noaa-afsc-mace/FSVPAD-hydrophones/Technical documentation/radioconfiguration/RX_1.png

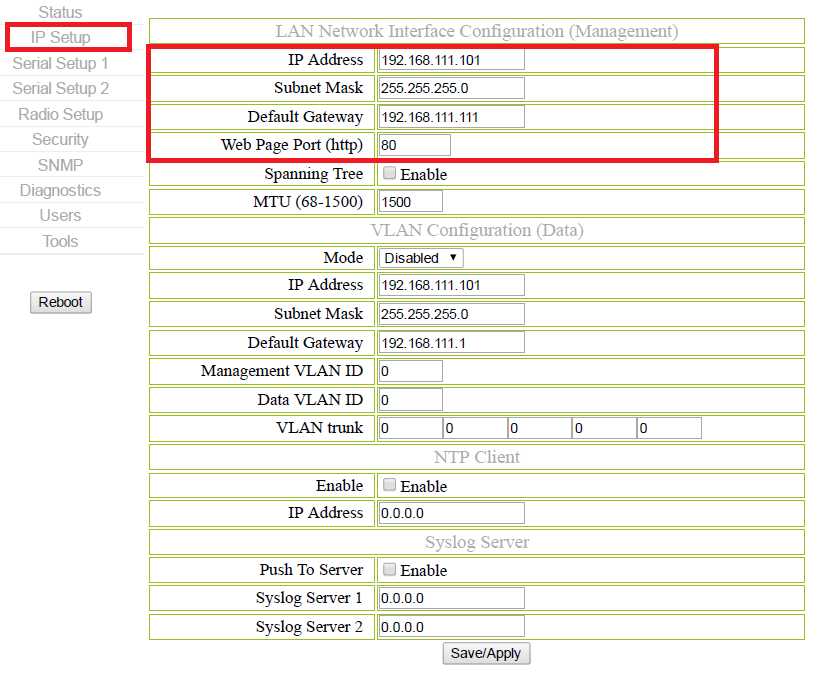
Technical documentation/radioconfiguration/RX_1.png
