noaa-afsc-mace/FSVPAD-hydrophones/Technical documentation/radioconfiguration/RX_2.png

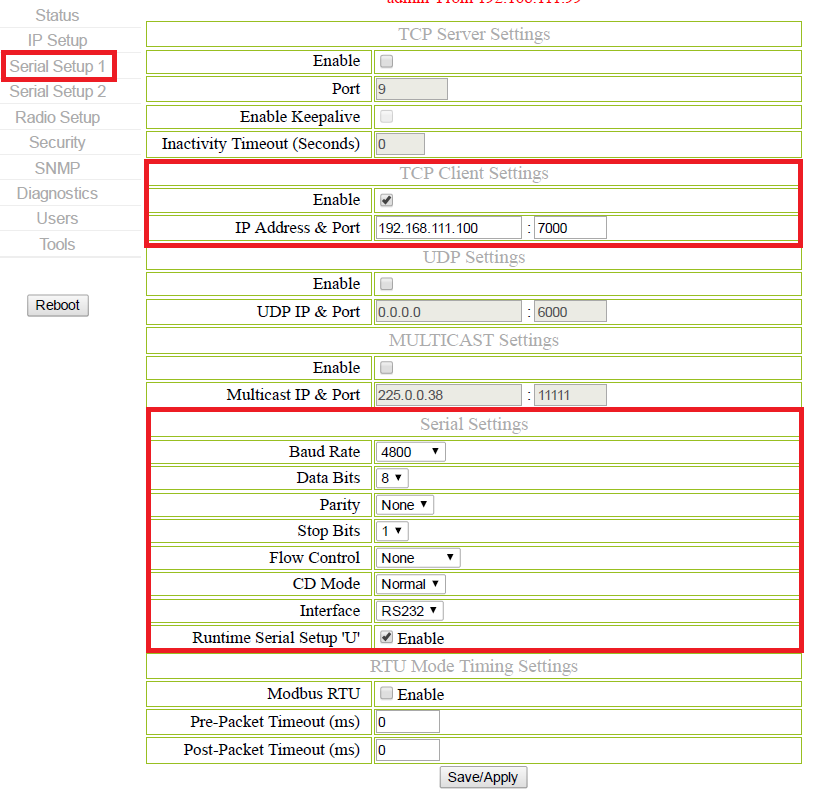
Technical documentation/radioconfiguration/RX_2.png
