noaa-afsc-mace/FSVPAD-hydrophones/Technical documentation/radioconfiguration/RX_3.png

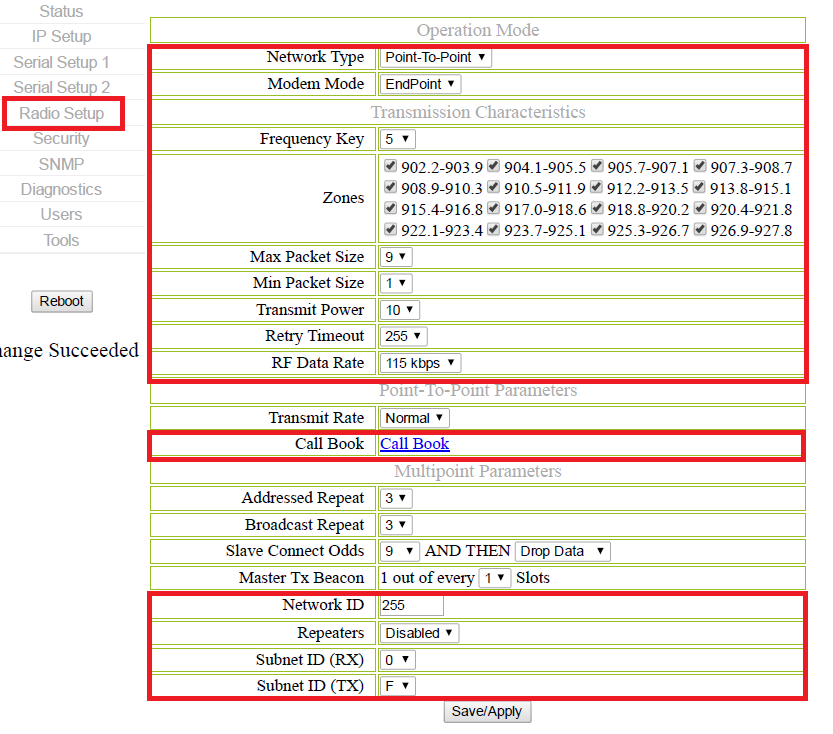
Technical documentation/radioconfiguration/RX_3.png
