noaa-afsc-mace/FSVPAD-hydrophones/Technical documentation/radioconfiguration/RX_4.png

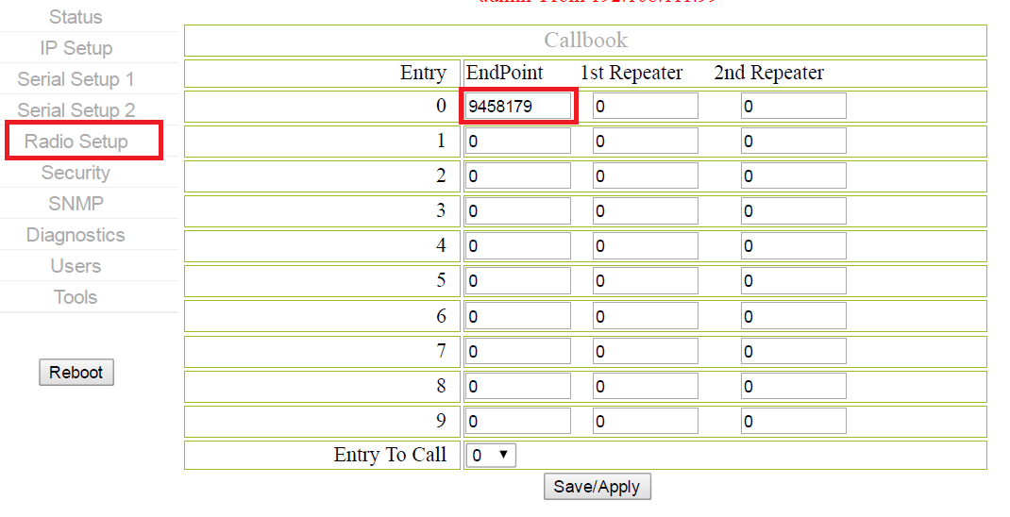
Technical documentation/radioconfiguration/RX_4.png
