noaa-afsc-mace/FSVPAD-hydrophones/Technical documentation/radioconfiguration/TX_1.png

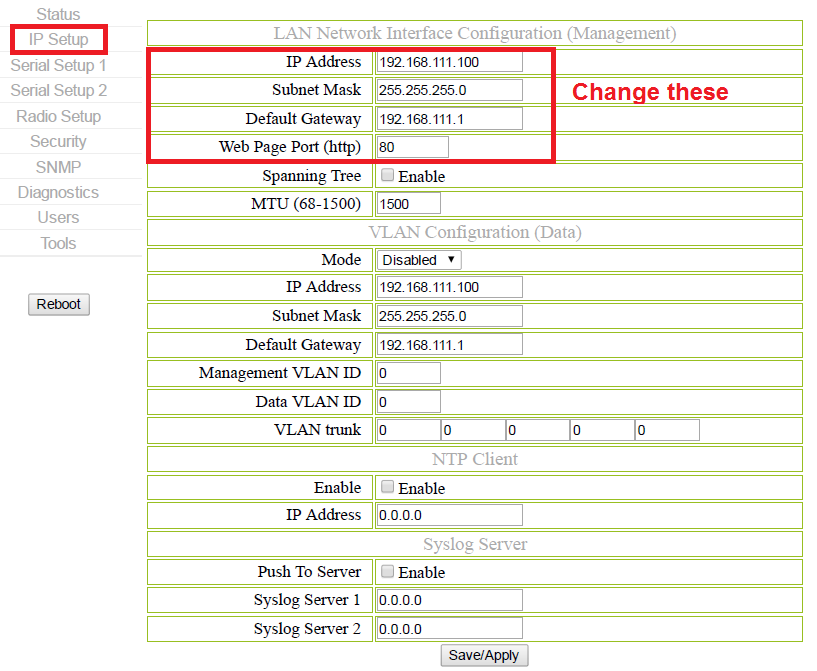
Technical documentation/radioconfiguration/TX_1.png
