noaa-afsc-mace/FSVPAD-hydrophones/Technical documentation/radioconfiguration/TX_2.png

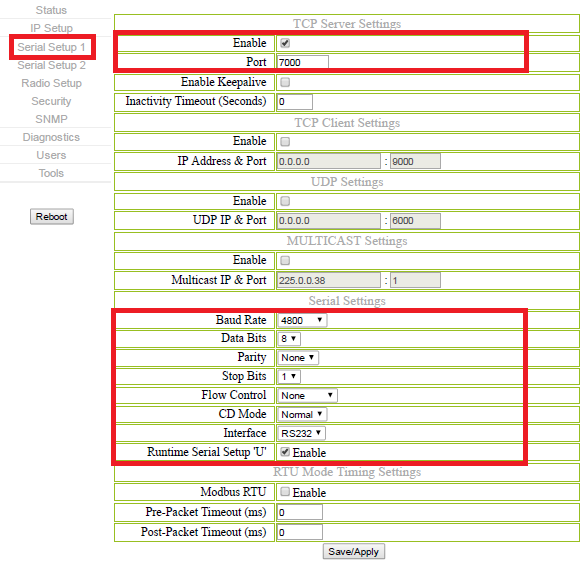
Technical documentation/radioconfiguration/TX_2.png
