noaa-afsc-mace/FSVPAD-hydrophones/Technical documentation/radioconfiguration/TX_3.png

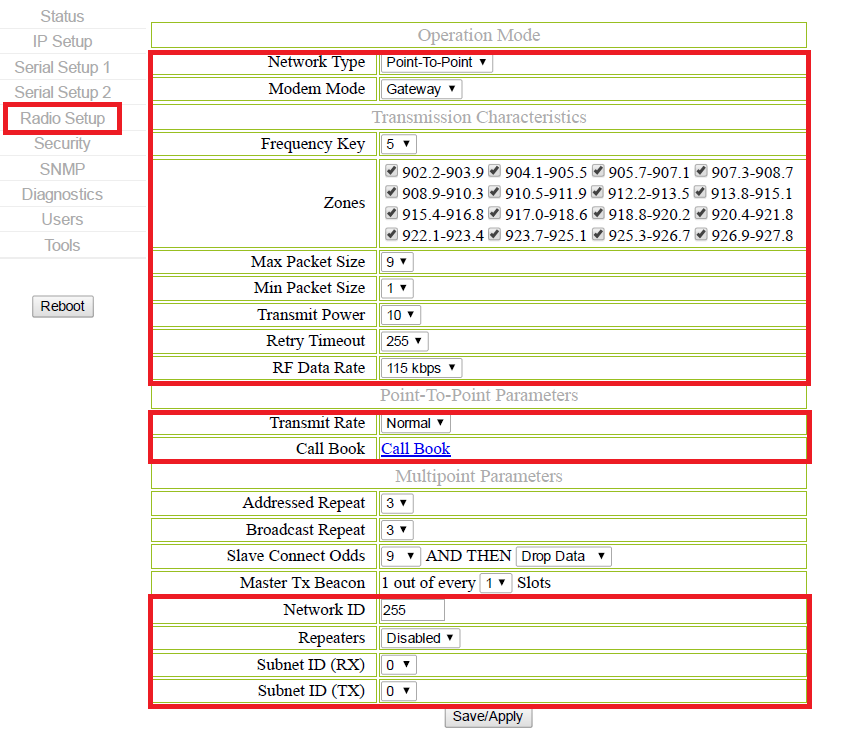
Technical documentation/radioconfiguration/TX_3.png
