noaa-afsc-mace/FSVPAD-hydrophones/Technical documentation/radioconfiguration/TX_4.png

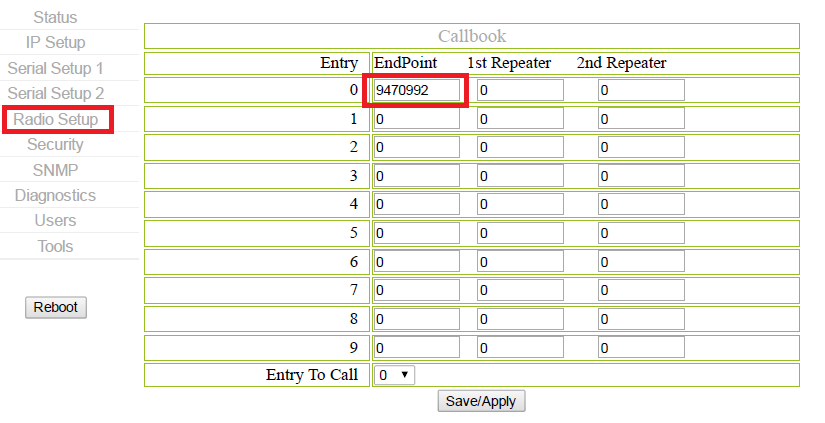
Technical documentation/radioconfiguration/TX_4.png
