noaa-afsc-mace/FSVPAD-hydrophones/Technical documentation/Subsystemdrawings/Electronics_side.png

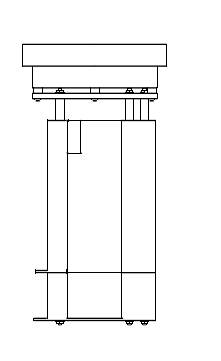
Technical documentation/Subsystemdrawings/Electronics_side.png
