noaa-afsc-mace/FSVPAD-hydrophones/Technical documentation/Subsystemdrawings/Mounting_Plate_noDims.png

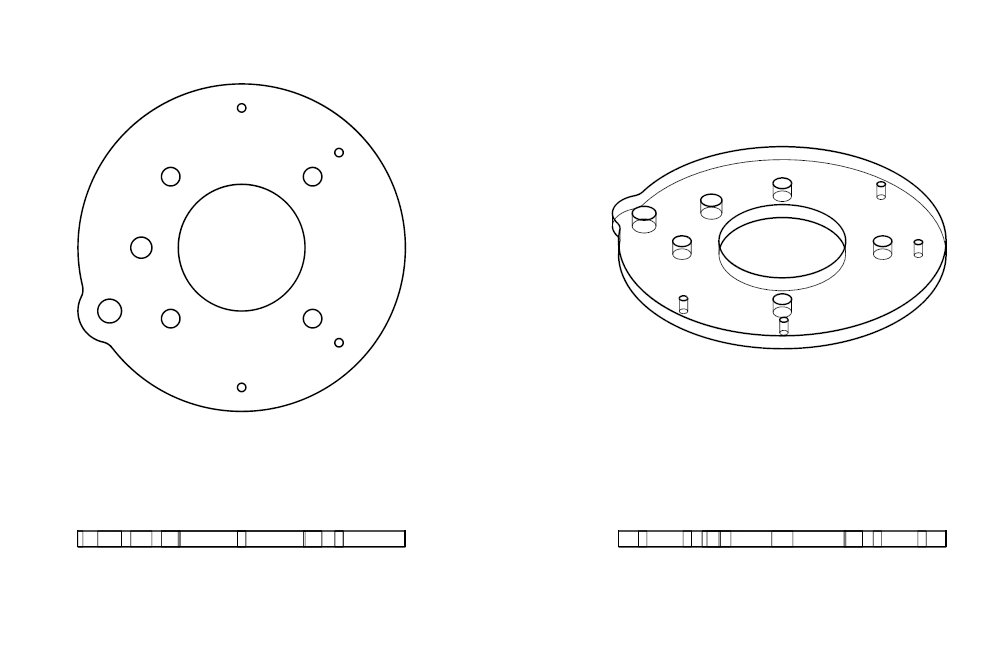
Technical documentation/Subsystemdrawings/Mounting_Plate_noDims.png
