noaa-afsc-mace/FSVPAD-hydrophones/Technical documentation/Subsystemdrawings/Sch 80 6 inch pipe flange.gif

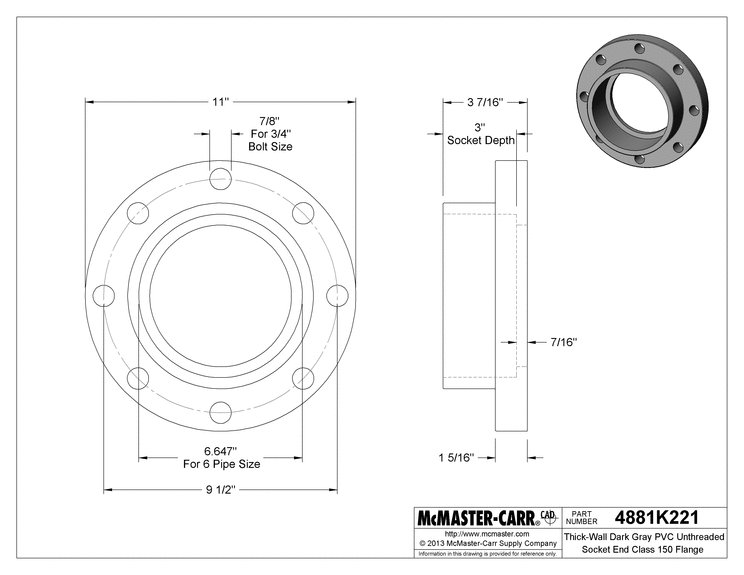
Technical documentation/Subsystemdrawings/Sch 80 6 inch pipe flange.gif
