noaa-afsc-mace/FSVPAD-hydrophones/Technical documentation/Subsystemdrawings/Strongback_Clamps.FCStd

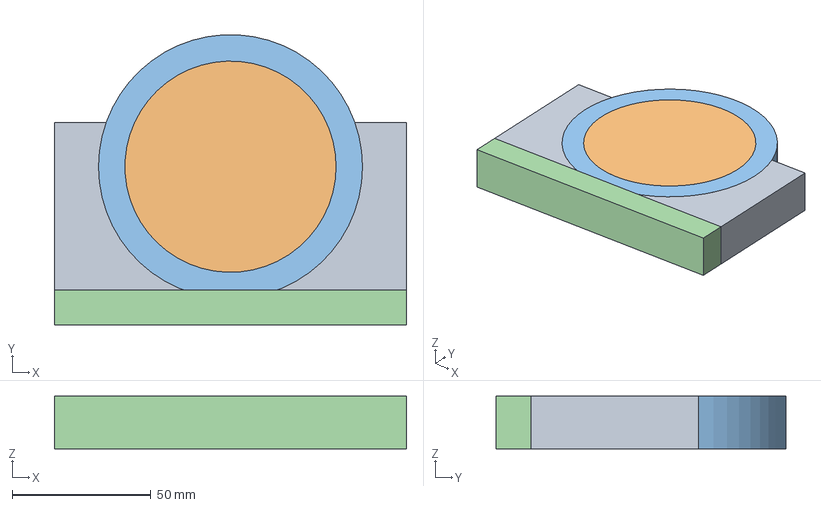
[picture p33: CAD file, 2024-04-29]
Technical documentation/Subsystemdrawings/Strongback_Clamps.FCStd
127.0 x 104.7 x 19.1 mm
Rectangle1
Cylindersmall
Cylinderlarge
