noaa-afsc-mace/FSVPAD-hydrophones/Technical documentation/Housingdrawings/HousingBot.stl

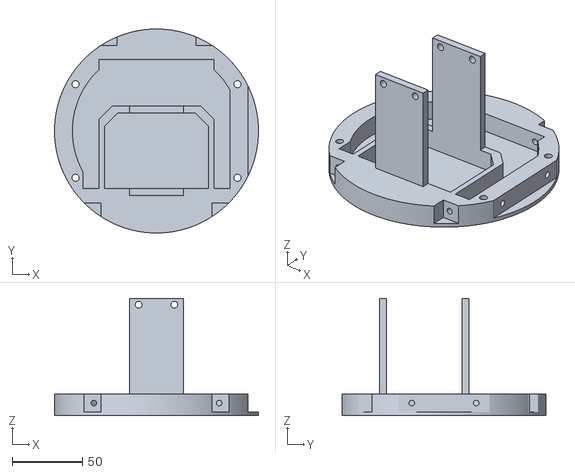
[picture p34: CAD file, 2024-04-29]
Technical documentation/Housingdrawings/HousingBot.stl
144.8 x 144.8 x 83.2
