noaa-afsc-mace/FSVPAD-hydrophones/Technical documentation/Subsystemdrawings/Strongback.FCStd

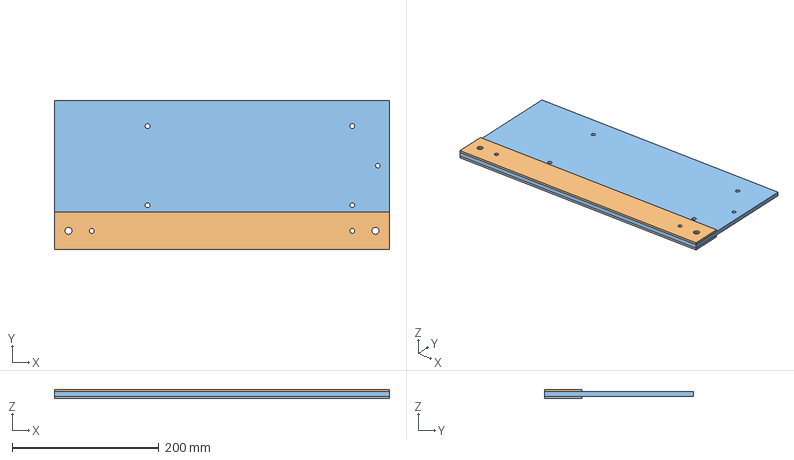
[picture p35: CAD file, 2024-04-29]
Technical documentation/Subsystemdrawings/Strongback.FCStd
457.2 x 203.2 x 12.7 mm
SS_holes1
SS_holes2
