noaa-afsc-mace/FSVPAD-hydrophones/Technical documentation/Housingdrawings/Top.stl

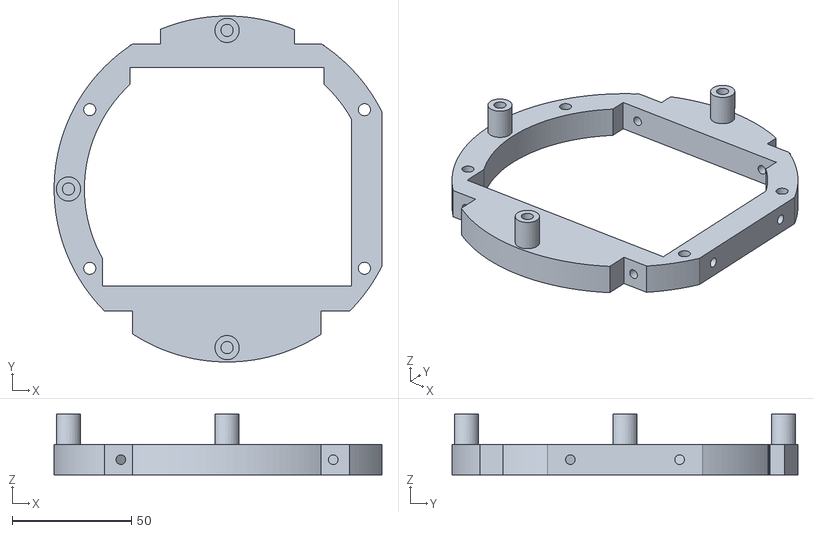
[picture p36: CAD file, 2024-04-29]
Technical documentation/Housingdrawings/Top.stl
137.1 x 144.8 x 25.4
