noaa-afsc-mace/FSVPAD-hydrophones/Technical documentation/Subsystemdrawings/Antenna_Stopper.FCStd

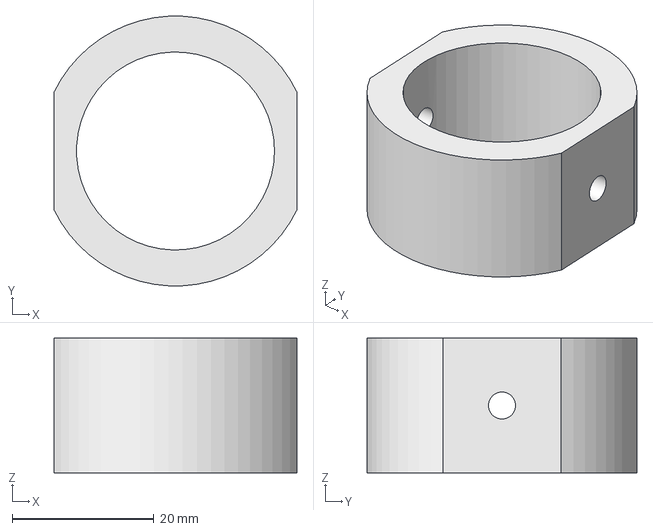
[picture p37: CAD file, 2024-04-29]
Technical documentation/Subsystemdrawings/Antenna_Stopper.FCStd
34.3 x 38.0 x 19.1 mm
