noaa-afsc-mace/FSVPAD-hydrophones/Technical documentation/Subsystemdrawings/LightFixtureB.FCStd

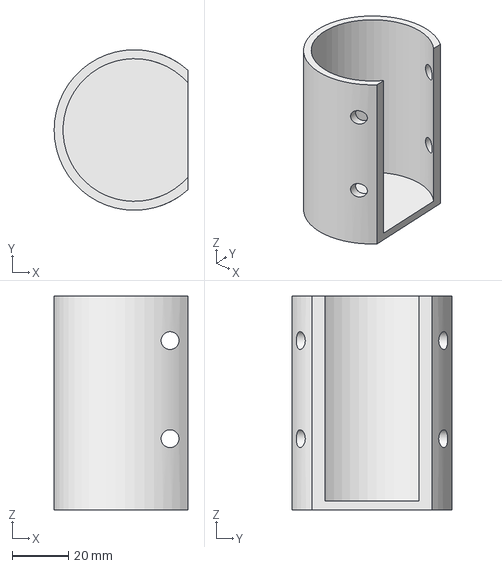
[picture p38: CAD file, 2024-04-29]
Technical documentation/Subsystemdrawings/LightFixtureB.FCStd
47.6 x 57.1 x 76.2 mm
