noaa-afsc-mace/FSVPAD-hydrophones/Technical documentation/Subsystemdrawings/Delrin_Cap.FCStd

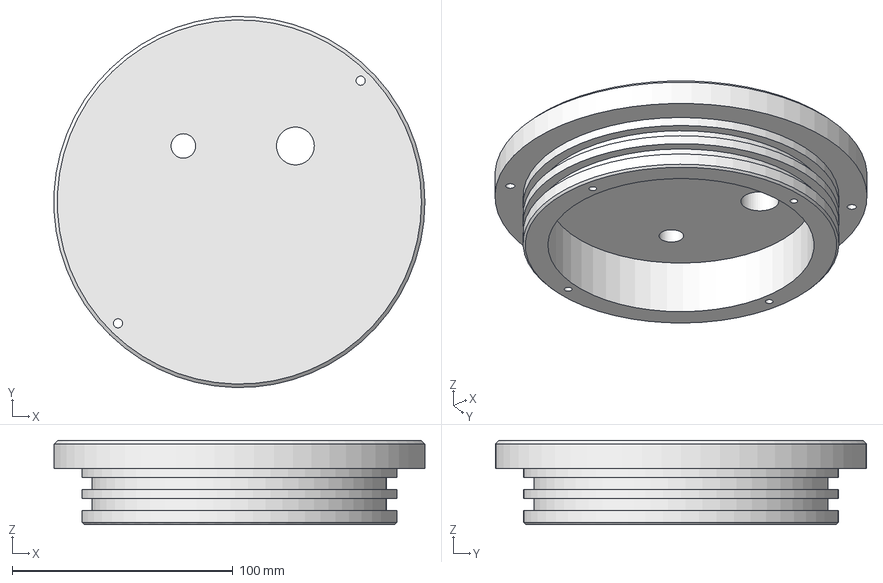
[picture p39: CAD file, 2024-04-29]
Technical documentation/Subsystemdrawings/Delrin_Cap.FCStd
168.2 x 168.2 x 38.1 mm
