noaa-afsc-mace/FSVPAD-hydrophones/Technical documentation/Subsystemdrawings/HeavePlate.FCStd

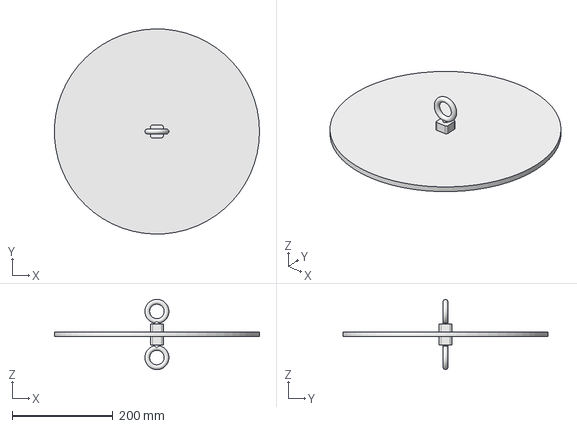
[picture p40: CAD file, 2024-04-29]
Technical documentation/Subsystemdrawings/HeavePlate.FCStd
406.1 x 406.3 x 139.1 mm
