noaa-afsc-mace/FSVPAD-hydrophones/Technical documentation/Subsystemdrawings/Strongback_Assesmbly_w_Clamps.FCStd

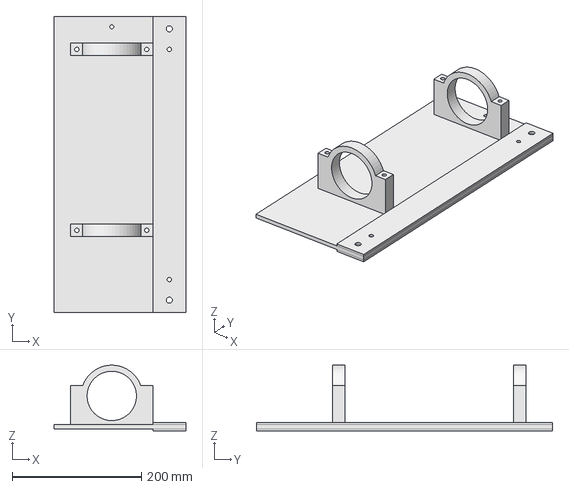
[picture p41: CAD file, 2024-04-29]
Technical documentation/Subsystemdrawings/Strongback_Assesmbly_w_Clamps.FCStd
203.2 x 457.2 x 101.6 mm
