noaa-afsc-mace/FSVPAD-hydrophones/Technical documentation/Subsystemdrawings/Strongback_Assesmbly_w_Clampsandhydrophones.FCStd

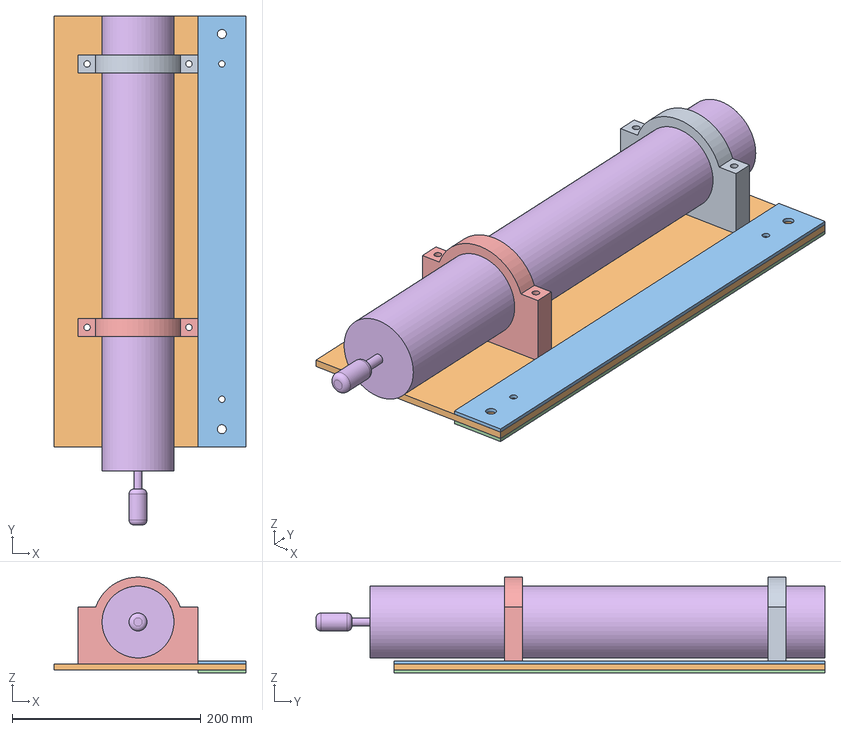
[picture p42: CAD file, 2024-04-29]
Technical documentation/Subsystemdrawings/Strongback_Assesmbly_w_Clampsandhydrophones.FCStd
203.2 x 539.8 x 101.6 mm
DelrinClamp
SS_holes2
SS_holes1
DelrinClamp2
Hydrophone
