noaa-afsc-mace/FSVPAD-hydrophones/Technical documentation/Subsystemdrawings/Exploded with light and antenna.FCStd

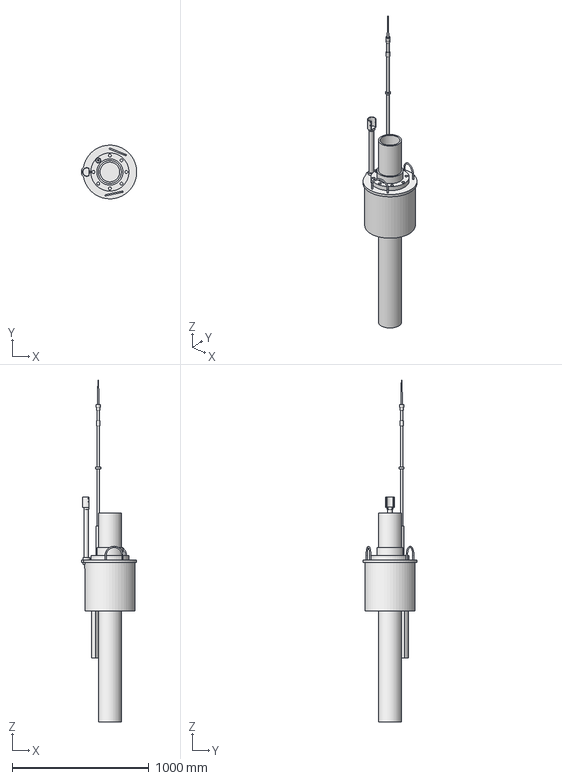
[picture p43: CAD file, 2024-04-29]
Technical documentation/Subsystemdrawings/Exploded with light and antenna.FCStd
406.4 x 393.4 x 2505.1 mm
