noaa-afsc-mace/FSVPAD-hydrophones/Technical documentation/Subsystemdrawings/Antenna_Top.FCStd

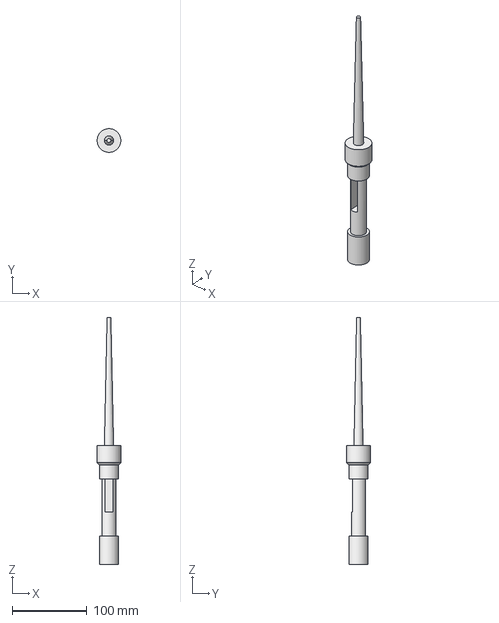
[picture p44: CAD file, 2024-04-29]
Technical documentation/Subsystemdrawings/Antenna_Top.FCStd
31.7 x 31.7 x 330.2 mm
