noaa-afsc-mace/FSVPAD-hydrophones/Technical documentation/Subsystemdrawings/Strongbacks_and_lines_SinglePoart.FCStd

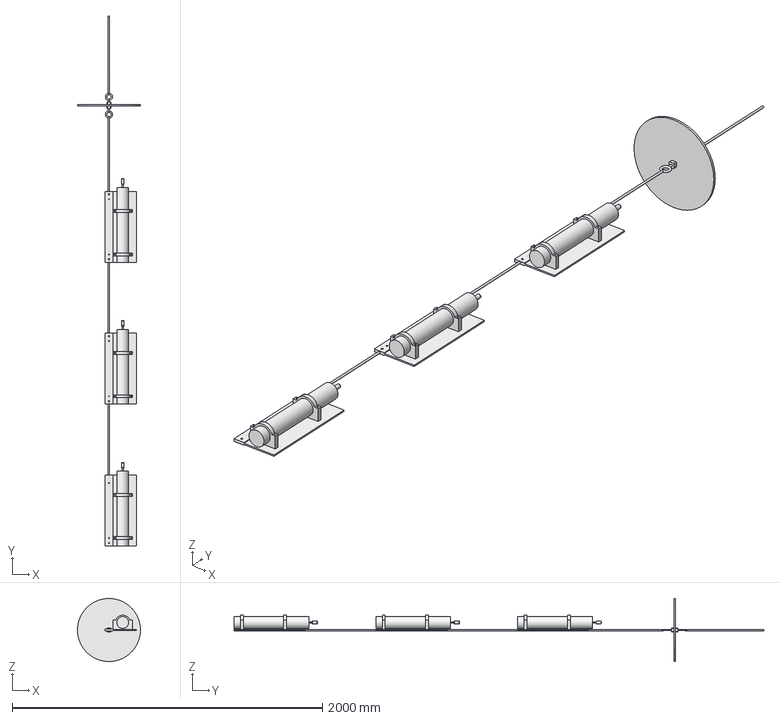
[picture p45: CAD file, 2024-04-29]
Technical documentation/Subsystemdrawings/Strongbacks_and_lines_SinglePoart.FCStd
406.0 x 3416.3 x 406.2 mm
