noaa-afsc-mace/FSVPAD-hydrophones/Technical documentation/Subsystemdrawings/MountingPlate.FCStd

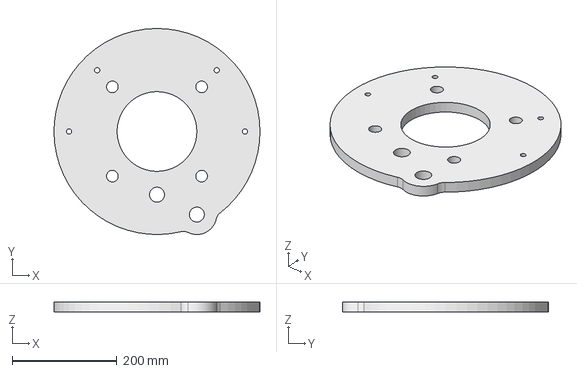
[picture p46: CAD file, 2024-04-29]
Technical documentation/Subsystemdrawings/MountingPlate.FCStd
393.7 x 393.7 x 19.1 mm
