noaa-afsc-mace/FSVPAD-hydrophones/Technical documentation/Subsystemdrawings/Strongback_Clamps2.FCStd

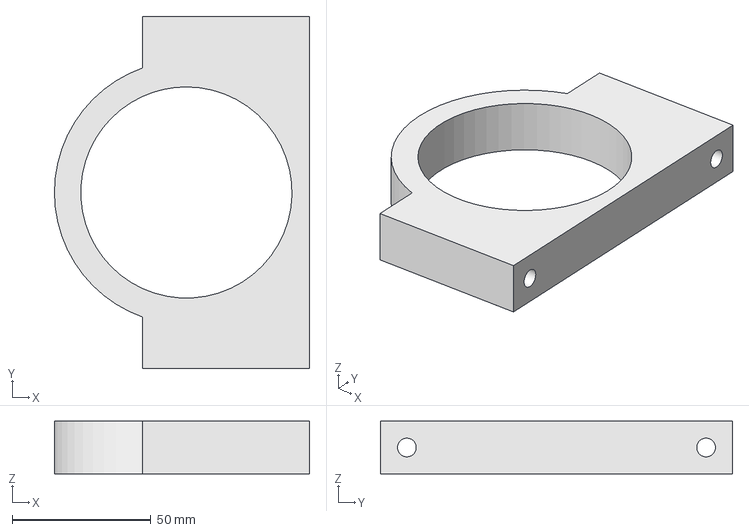
[picture p47: CAD file, 2024-04-29]
Technical documentation/Subsystemdrawings/Strongback_Clamps2.FCStd
92.1 x 127.0 x 19.1 mm
