noaa-afsc-mace/FSVPAD-hydrophones/Technical documentation/Subsystemdrawings/Antenna_PipeFoam.FCStd

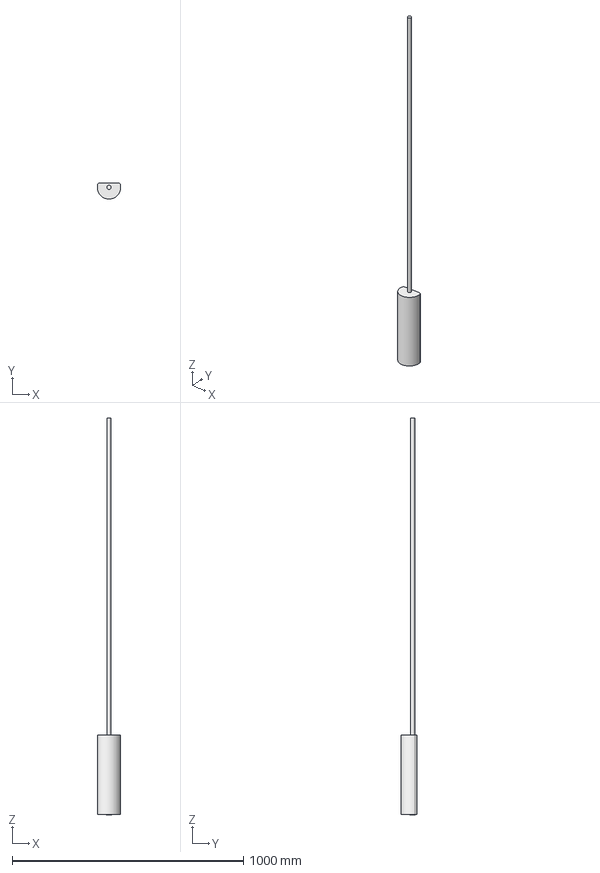
[picture p48: CAD file, 2024-04-29]
Technical documentation/Subsystemdrawings/Antenna_PipeFoam.FCStd
101.6 x 69.8 x 1717.0 mm
