noaa-afsc-mace/FSVPAD-hydrophones/Technical documentation/Subsystemdrawings/LightFixtureStopper.FCStd

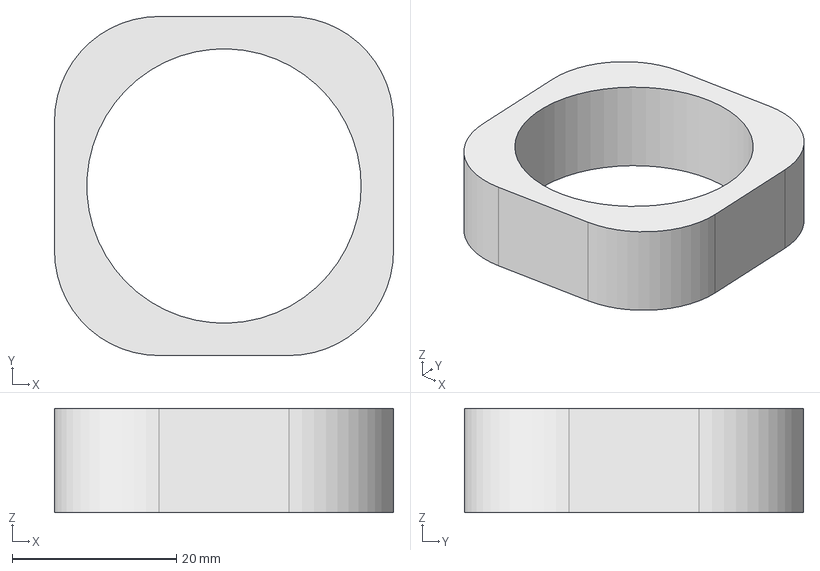
[picture p49: CAD file, 2024-04-29]
Technical documentation/Subsystemdrawings/LightFixtureStopper.FCStd
41.3 x 41.3 x 12.7 mm
