noaa-afsc-mace/FSVPAD-hydrophones/Example results/Ambient_vs_CPA.png

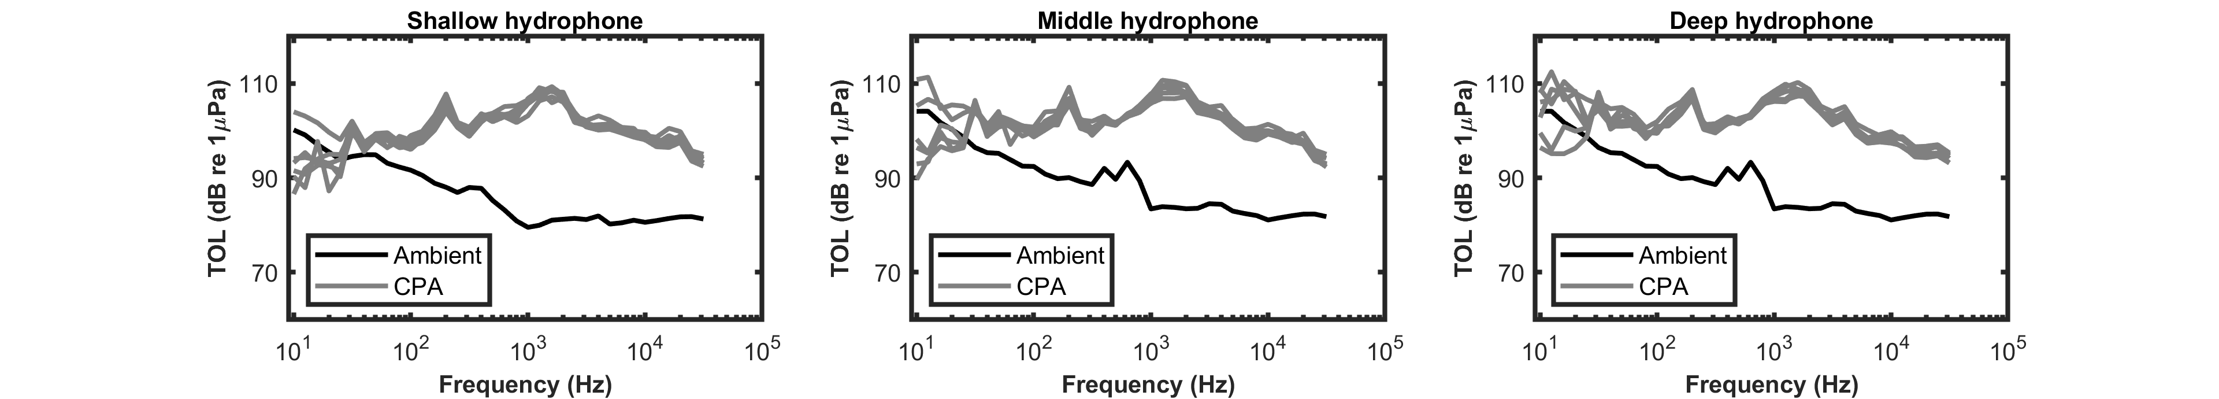
Example results/Ambient_vs_CPA.png
