noaa-afsc-mace/FSVPAD-hydrophones/Example results/CPA_and_TOL.png

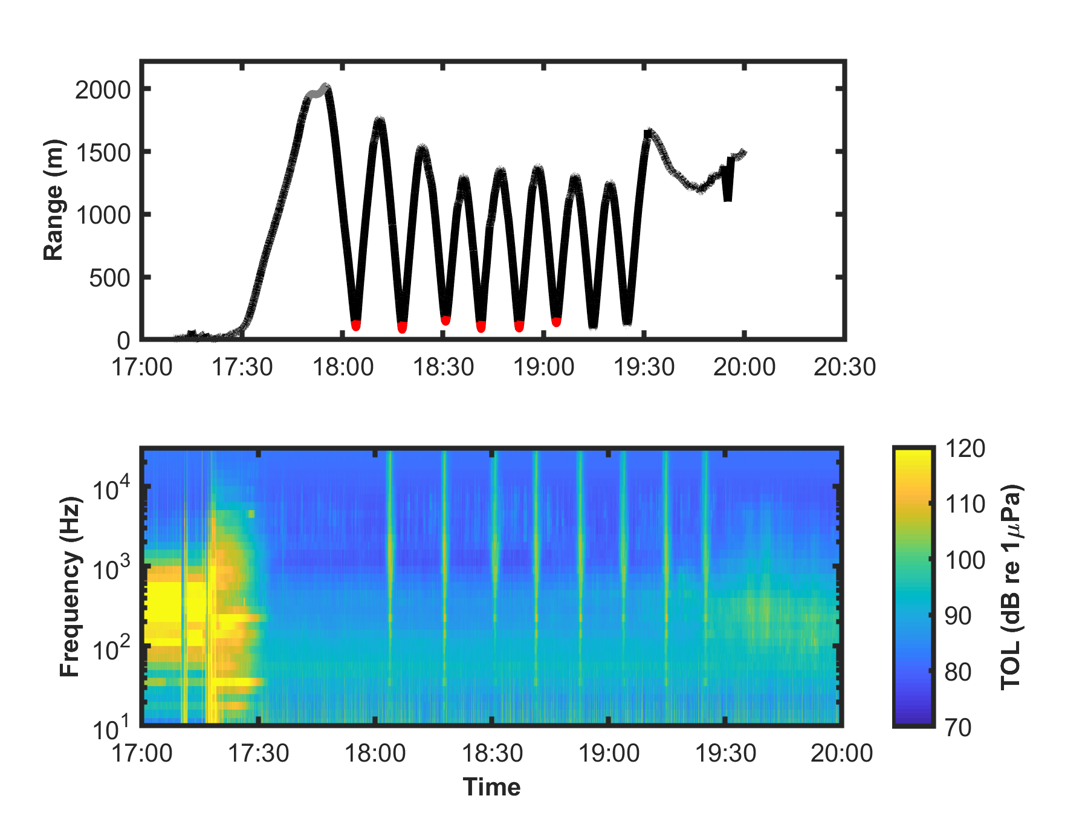
Example results/CPA_and_TOL.png
