noaa-afsc-mace/FSVPAD-hydrophones/Example results/DY_11knot_radiated_noise_comparison.png

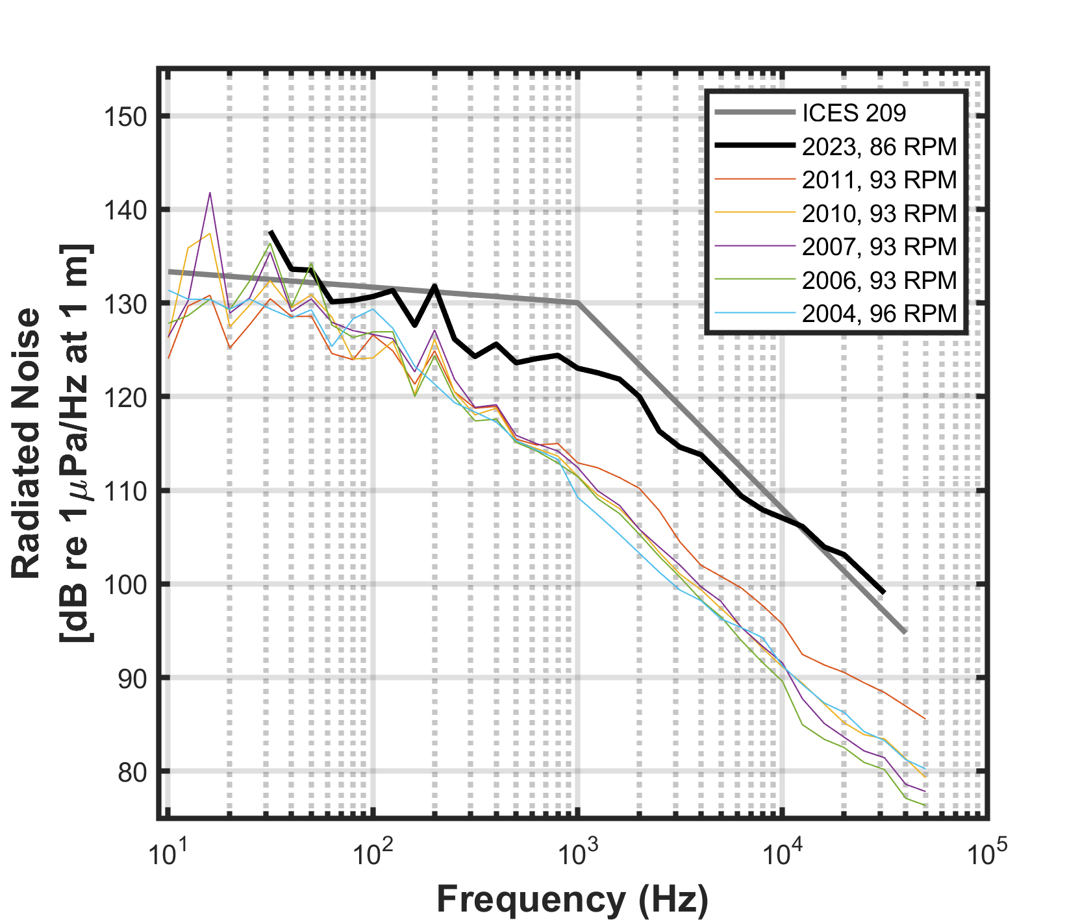
Example results/DY_11knot_radiated_noise_comparison.png
