noaa-afsc-mace/FSVPAD-hydrophones/Example results/FORMAL_Noise_Test_SNRs.png

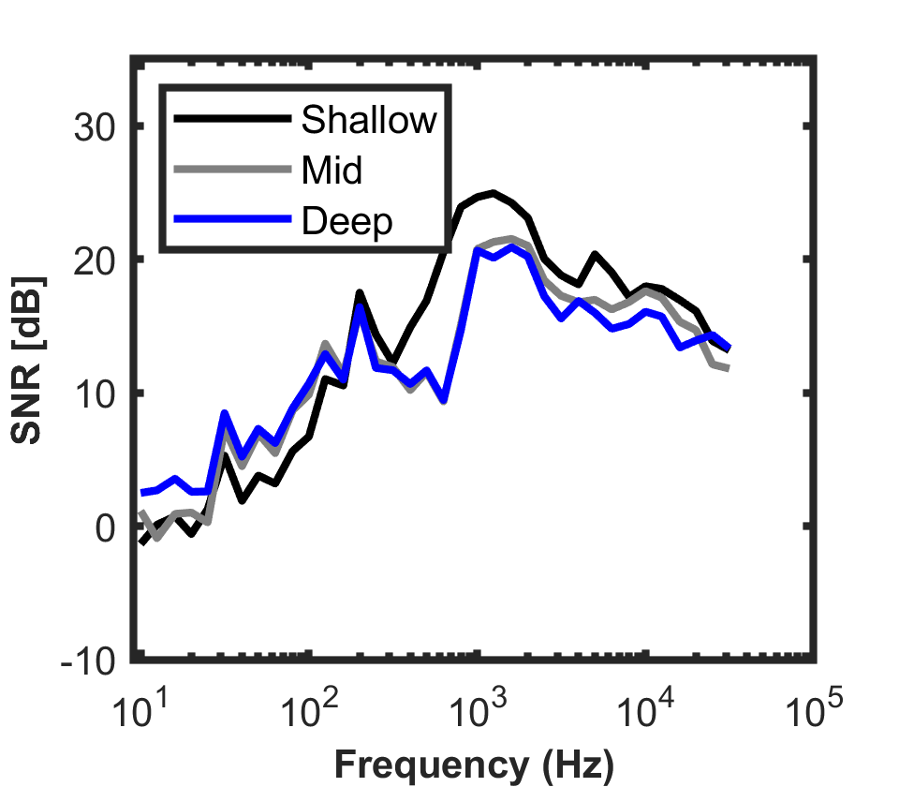
Example results/FORMAL_Noise_Test_SNRs.png
