noaa-afsc-mace/FSVPAD-hydrophones/Example results/FORMAL_Radiated_Noise.png

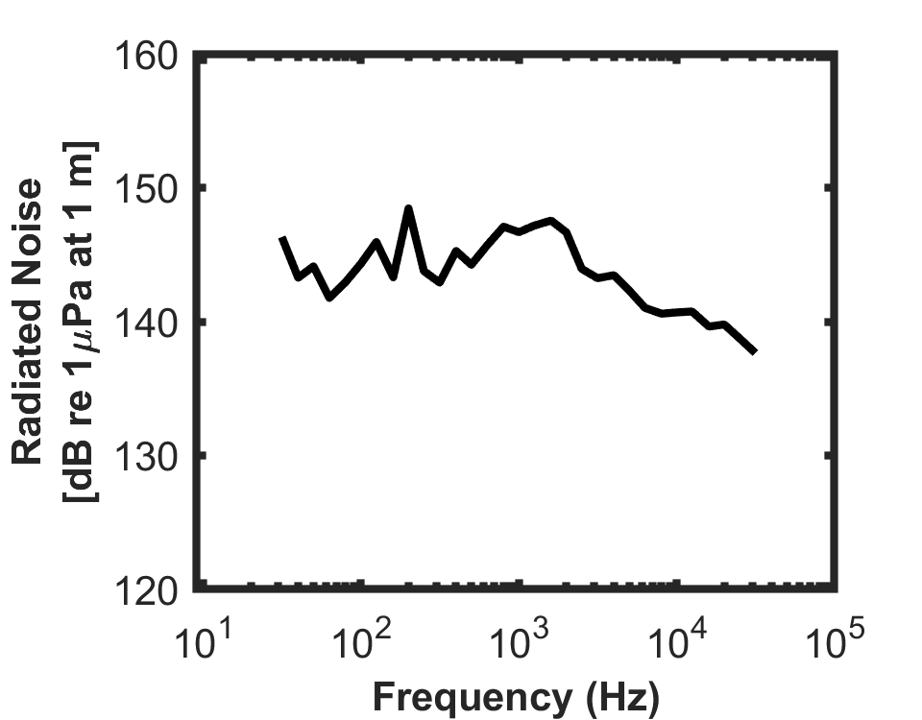
Example results/FORMAL_Radiated_Noise.png
