noaa-afsc-mace/FSVPAD-hydrophones/Example results/Noise_Test_SNRs.png

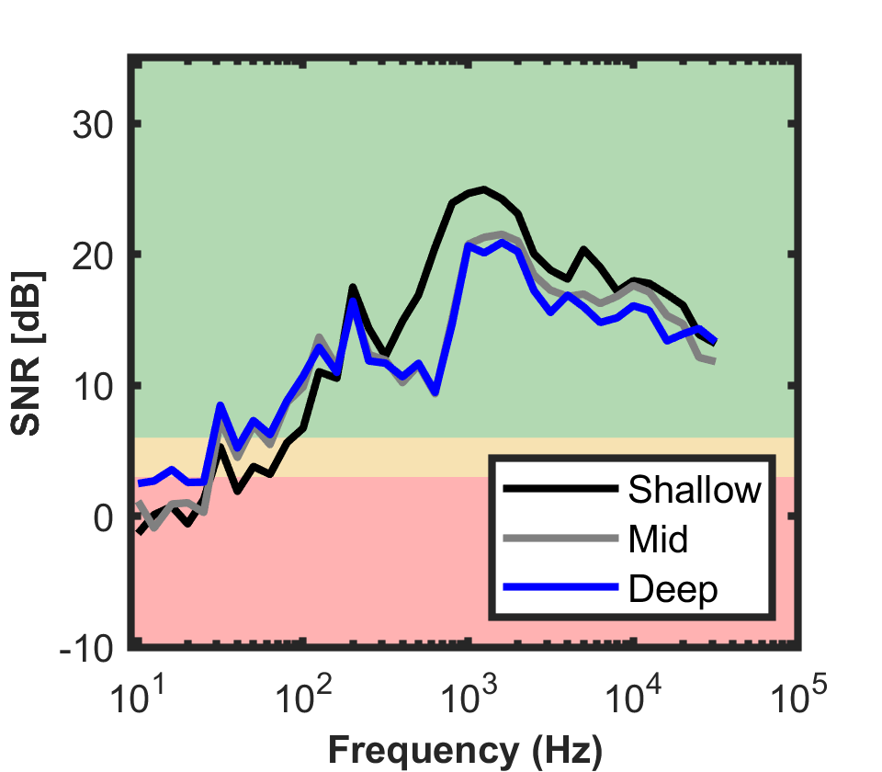
Example results/Noise_Test_SNRs.png
