noaa-afsc-mace/FSVPAD-hydrophones/Example results/RadiatedNoise_All_Passes.png

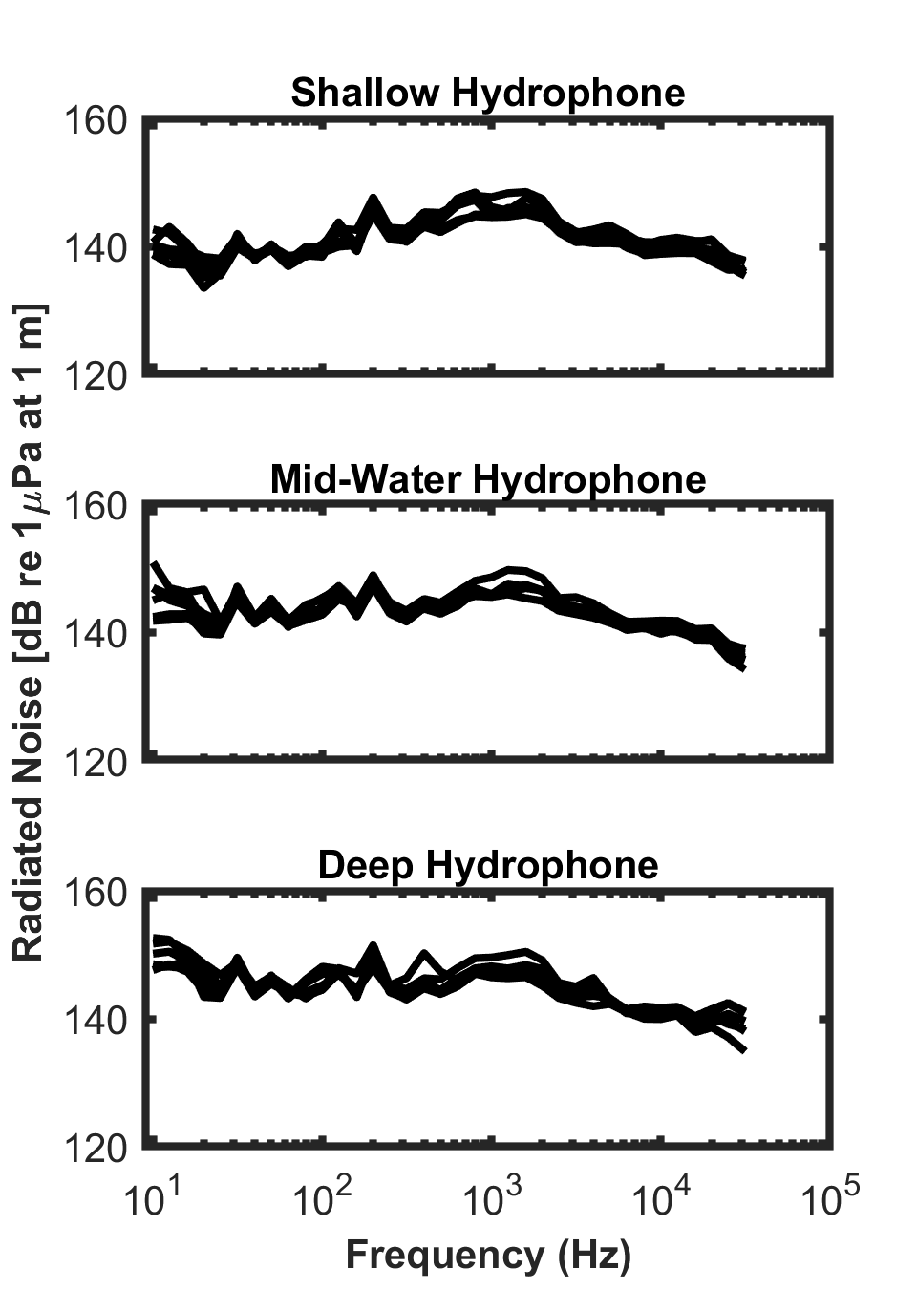
Example results/RadiatedNoise_All_Passes.png
