noaa-afsc-mace/FSVPAD-hydrophones/Example results/Range_of_Noise.png

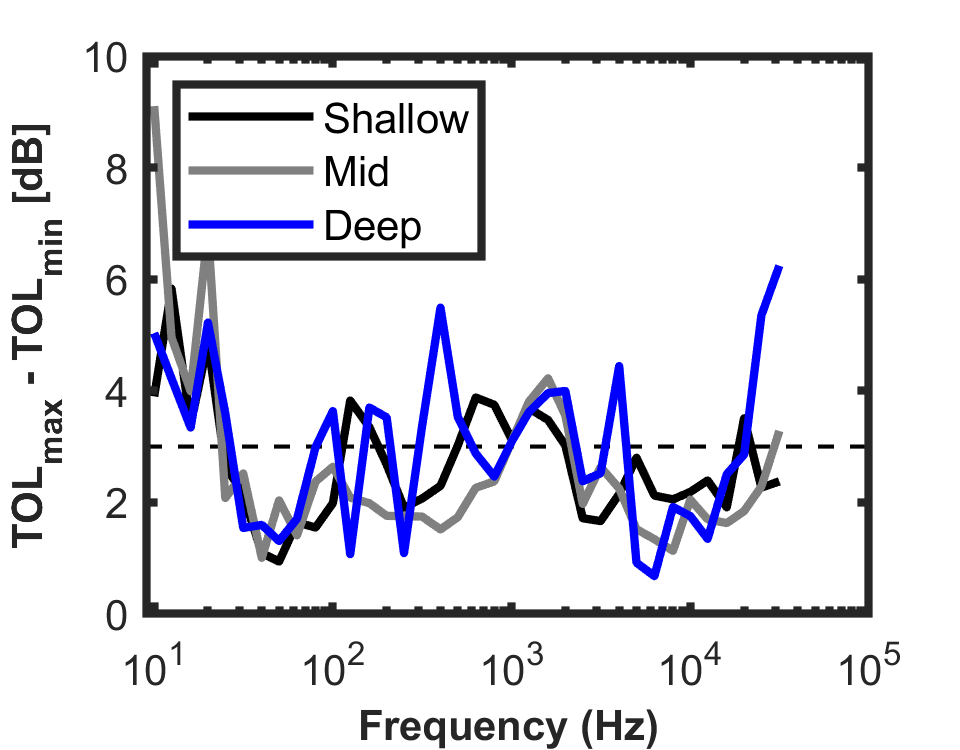
Example results/Range_of_Noise.png
