noaa-afsc-mace/FSVPAD-hydrophones/Example results/Result_overview_vs_ICES_SPEC.png

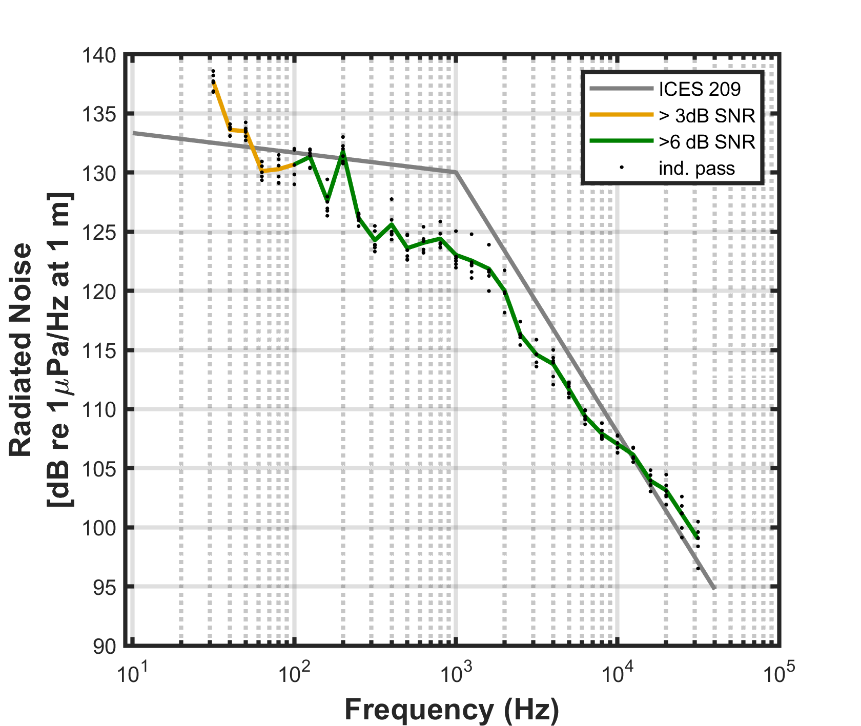
Example results/Result_overview_vs_ICES_SPEC.png
