noaa-afsc-mace/FSVPAD-hydrophones/Technical documentation/PistonphoneCalibration/SN_382313_Cal_TimeSeries.png

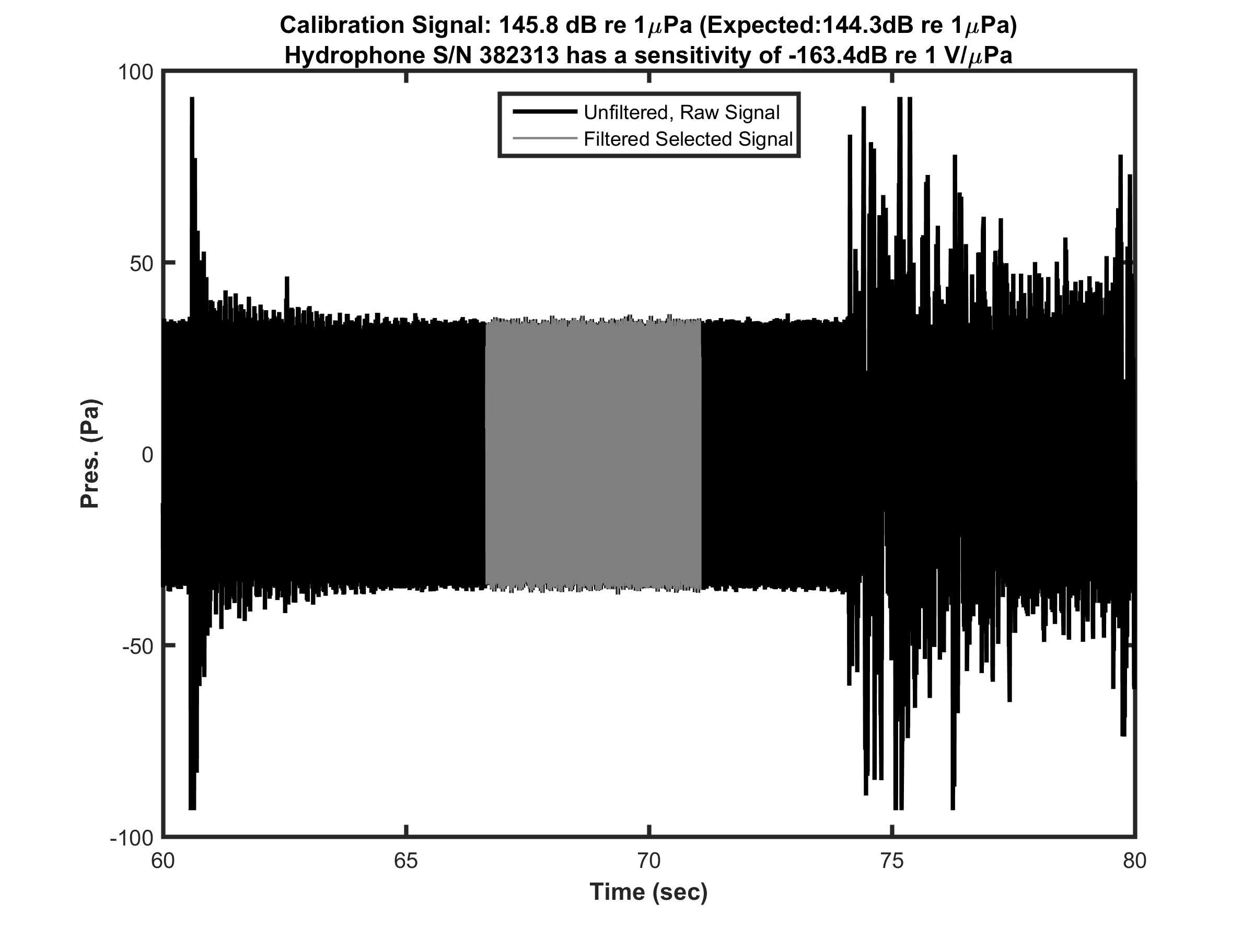
Technical documentation/PistonphoneCalibration/SN_382313_Cal_TimeSeries.png
