noaa-afsc-mace/FSVPAD-hydrophones/Technical documentation/Subsystemdrawings/Full_Assembly2.pdf

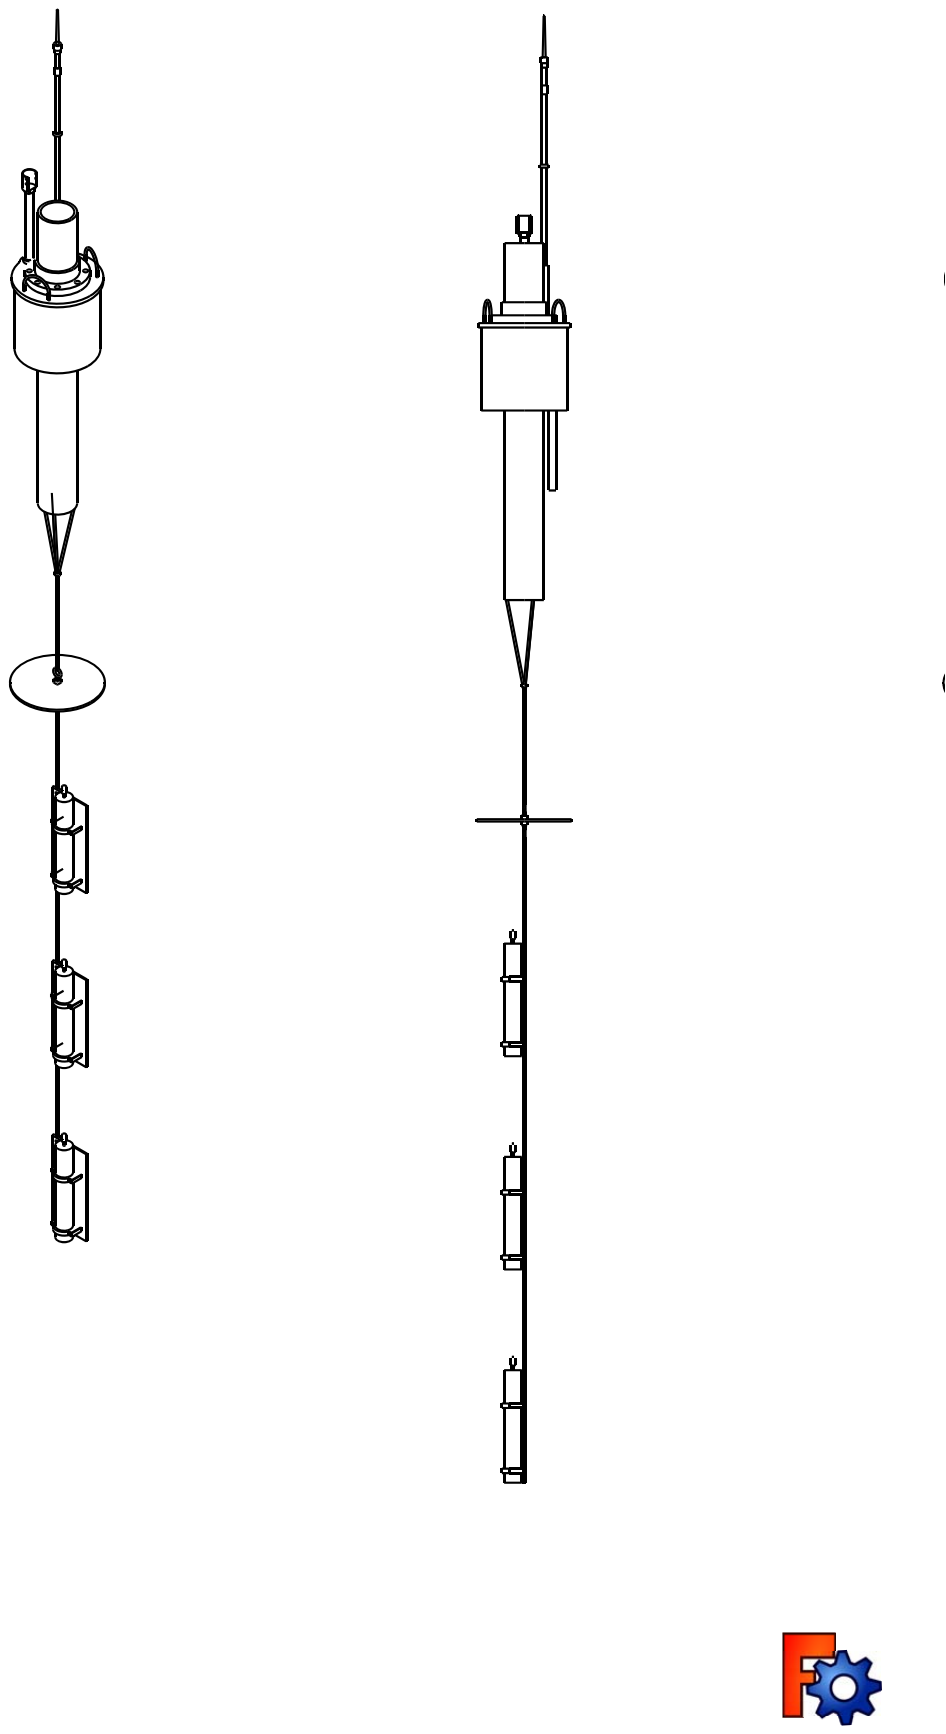
[picture p71: page 1]
