noaa-afsc-mace/FSVPAD-hydrophones/Technical documentation/Subsystemdrawings/Spar Assembly 2.pdf

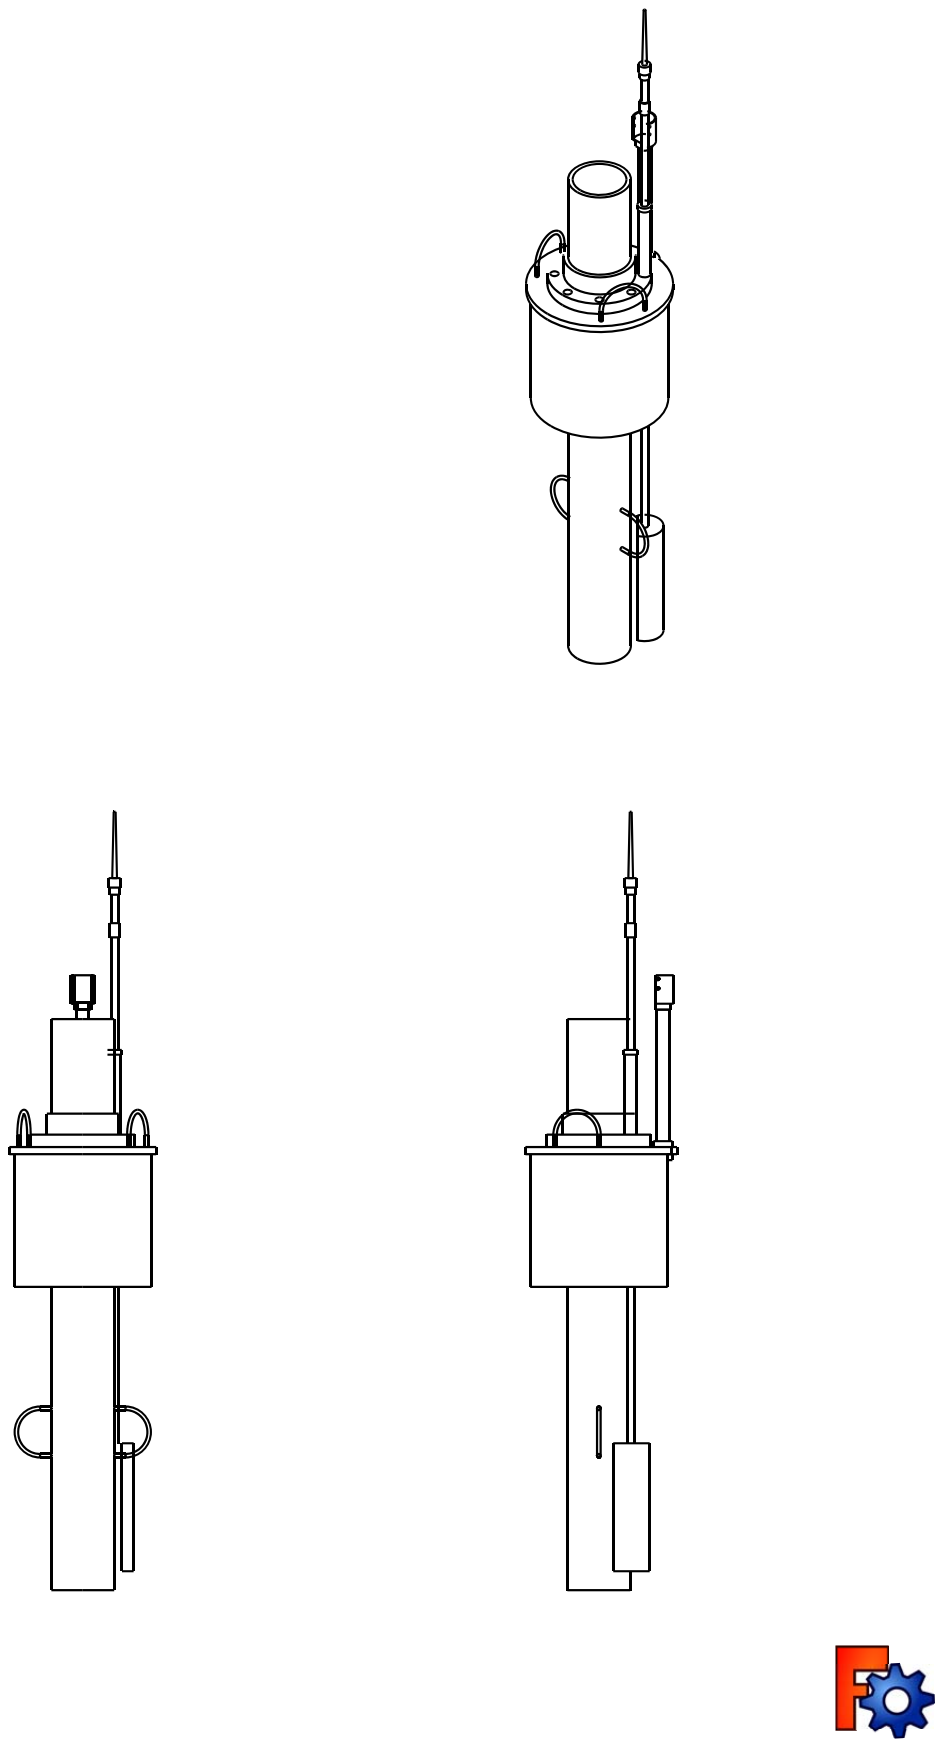
[picture p72: page 1]
