noaa-afsc-mace/FSVPAD-hydrophones/Technical documentation/Subsystemdrawings/Spar Assembly.pdf

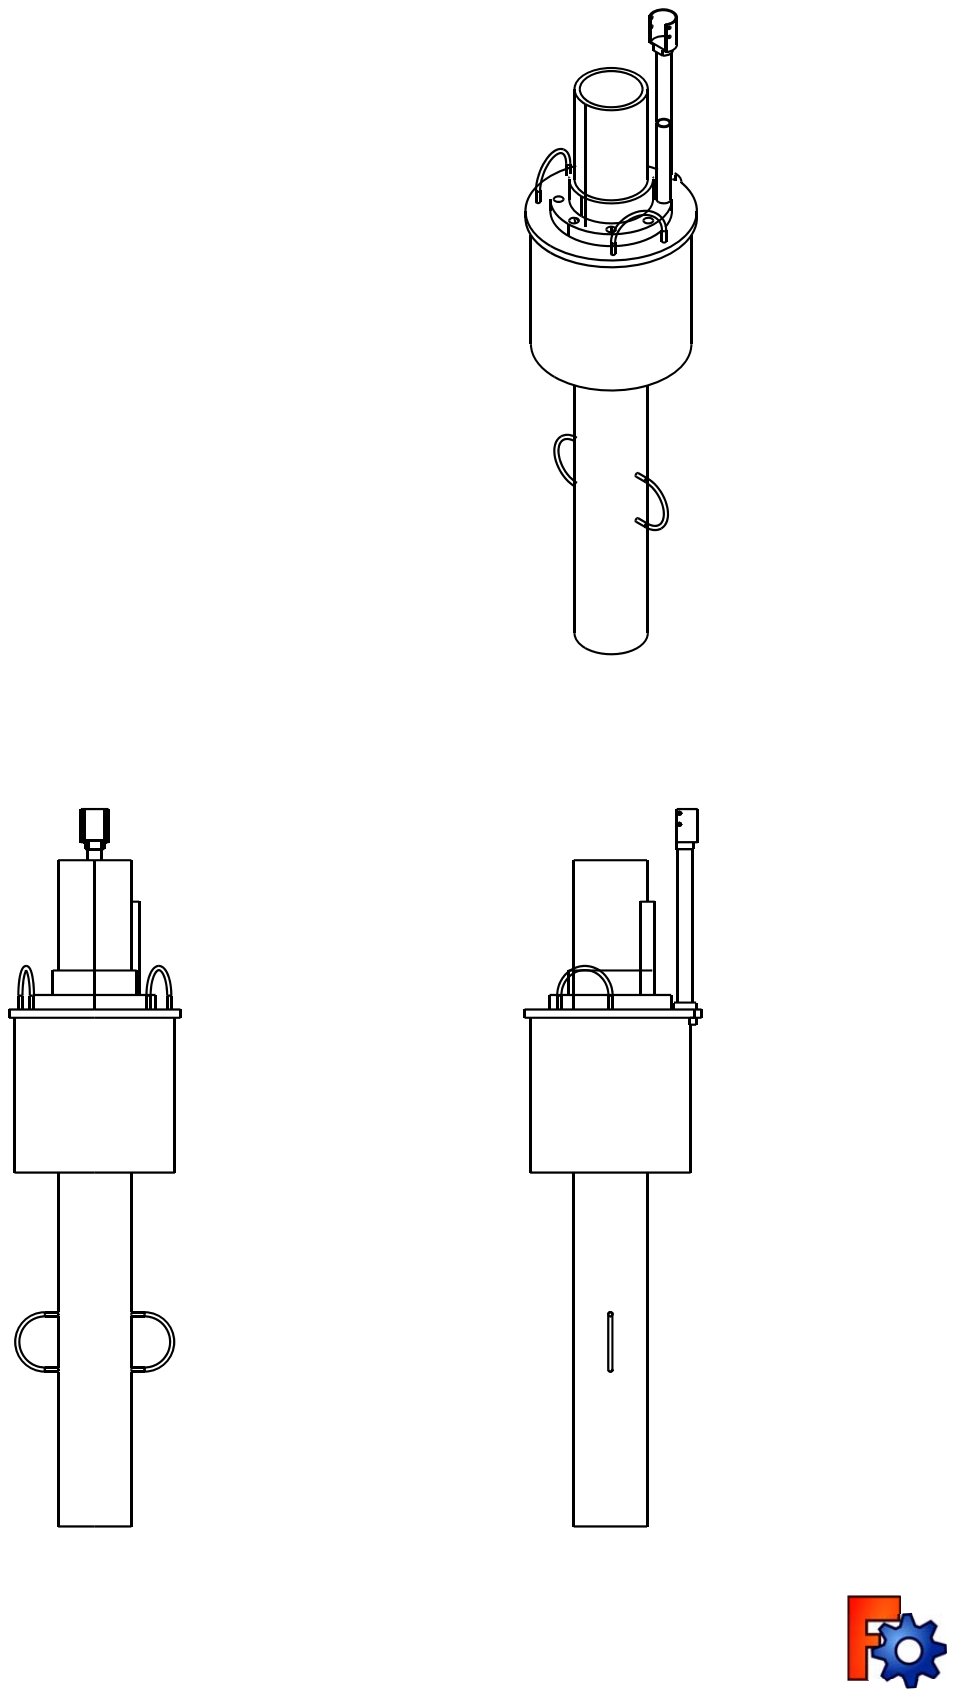
[picture p73: page 1]
