noaa-afsc-mace/FSVPAD-hydrophones/Technical documentation/Subsystemdrawings/Strongback Assembly.pdf

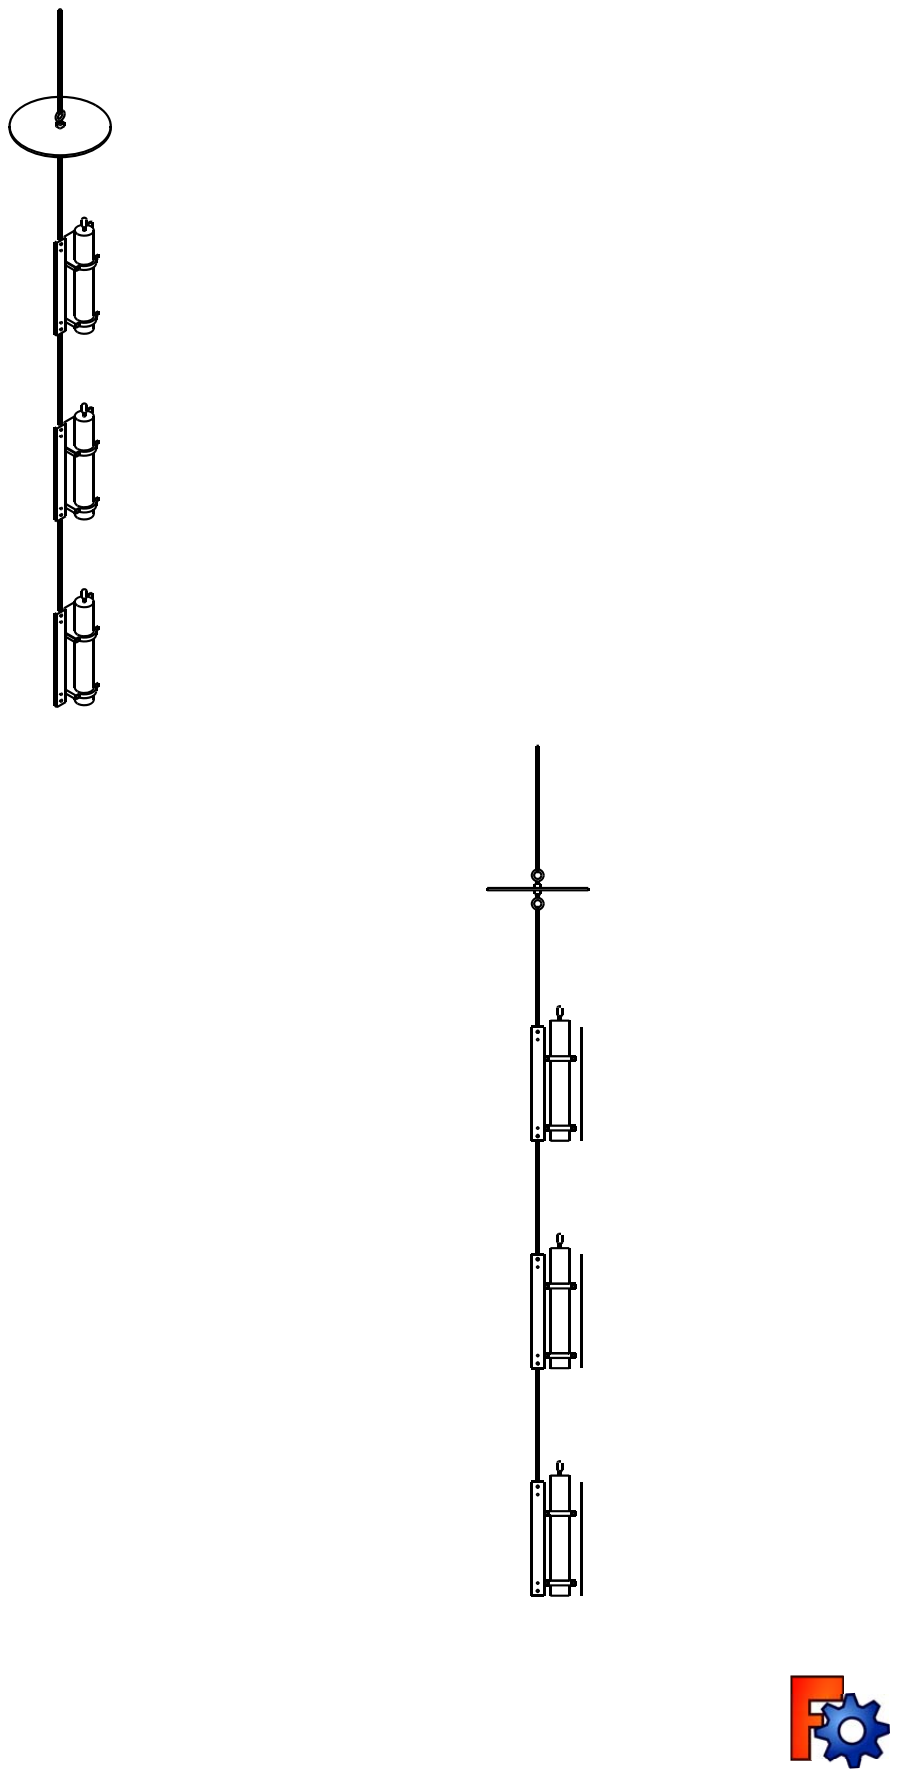
[picture p74: page 1]
