noaa-afsc-mace/FSVPAD-hydrophones/Technical documentation/Subsystemdrawings/Antenna_PipeFoam.pdf

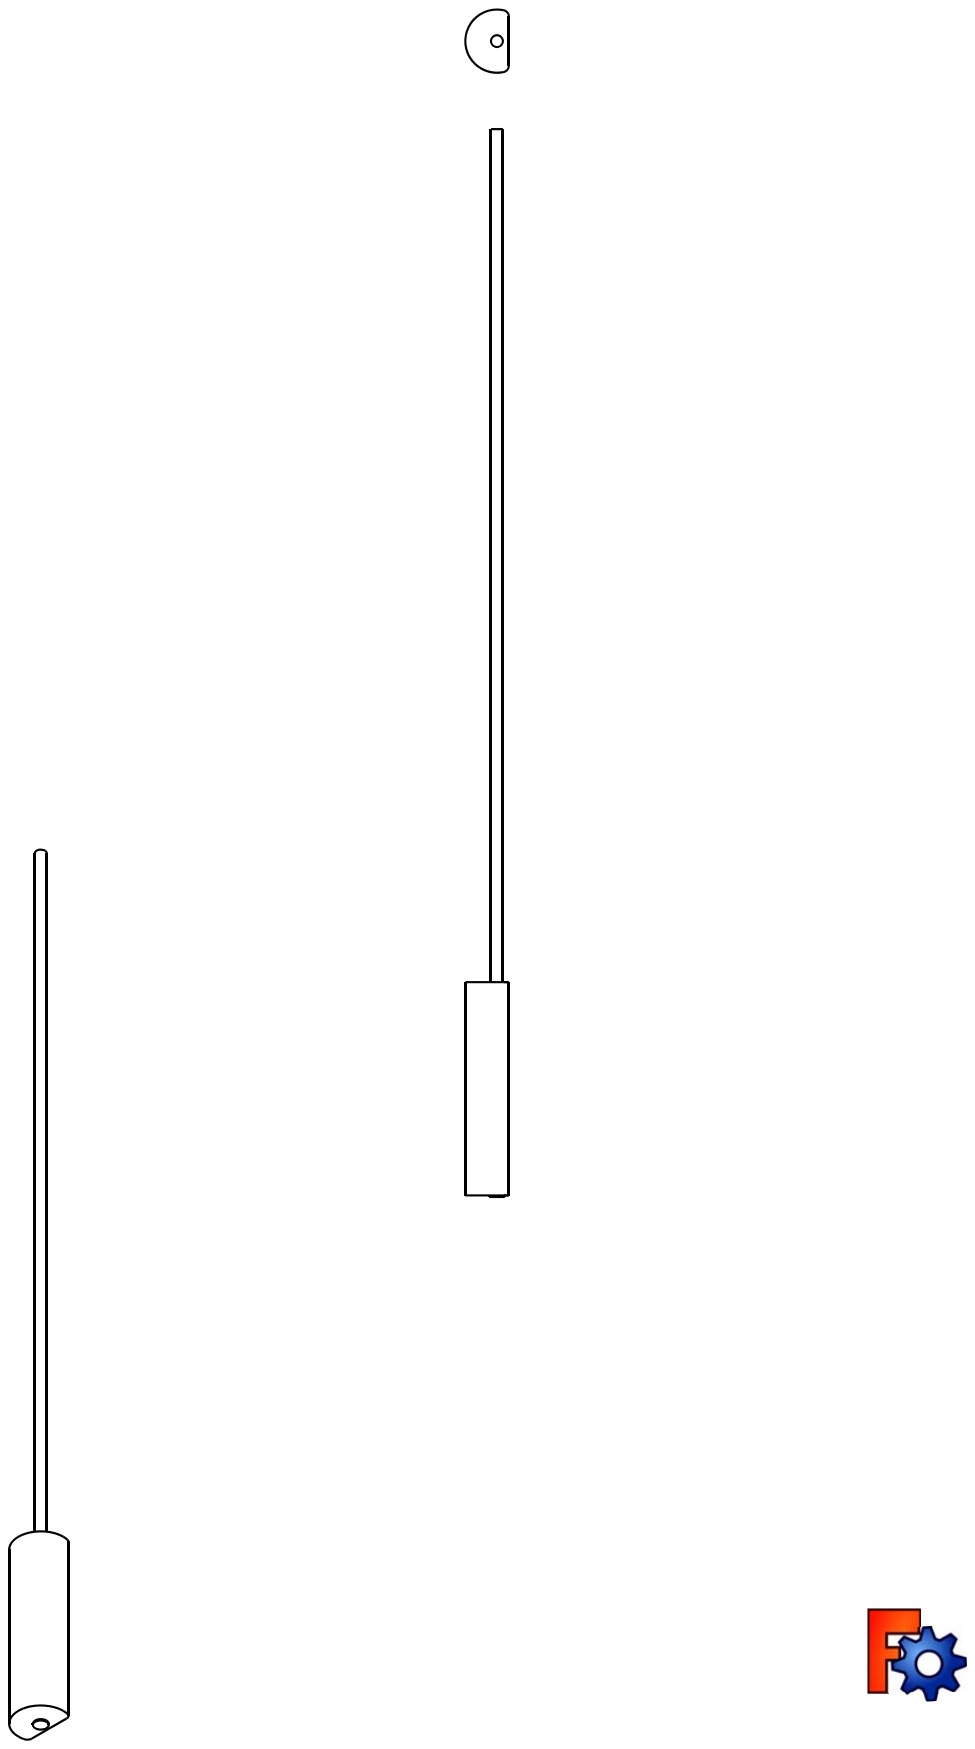
[picture p75: page 1]
