noaa-afsc-mace/FSVPAD-hydrophones/Technical documentation/Subsystemdrawings/Antenna_Stopper.pdf

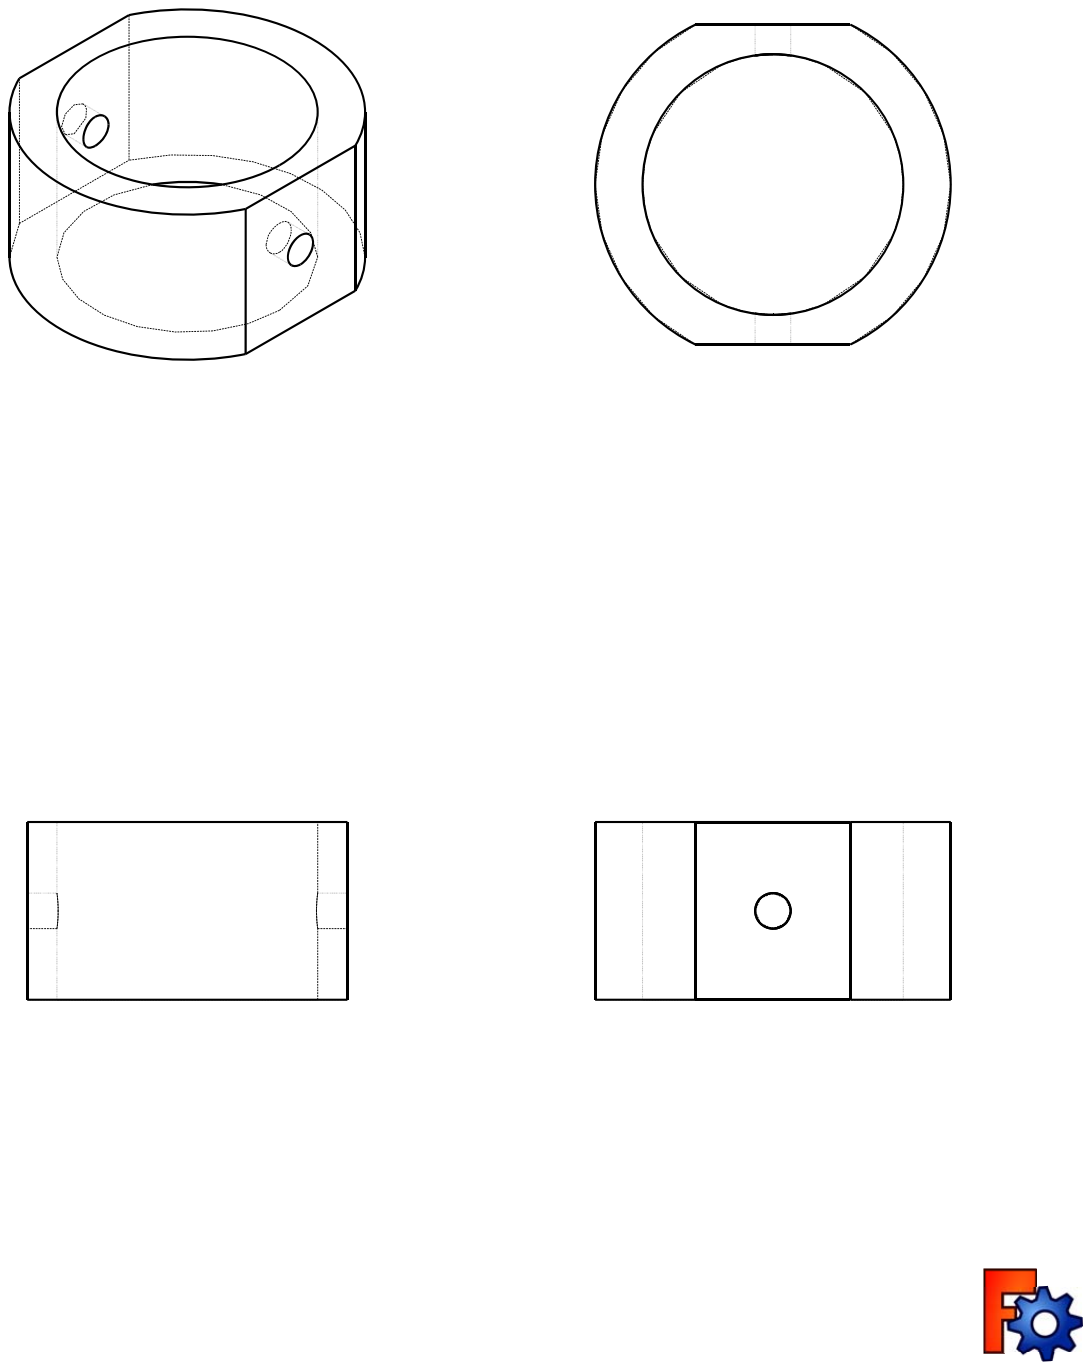
[picture p76: page 1]
