noaa-afsc-mace/FSVPAD-hydrophones/Technical documentation/Subsystemdrawings/AntennaTop.pdf

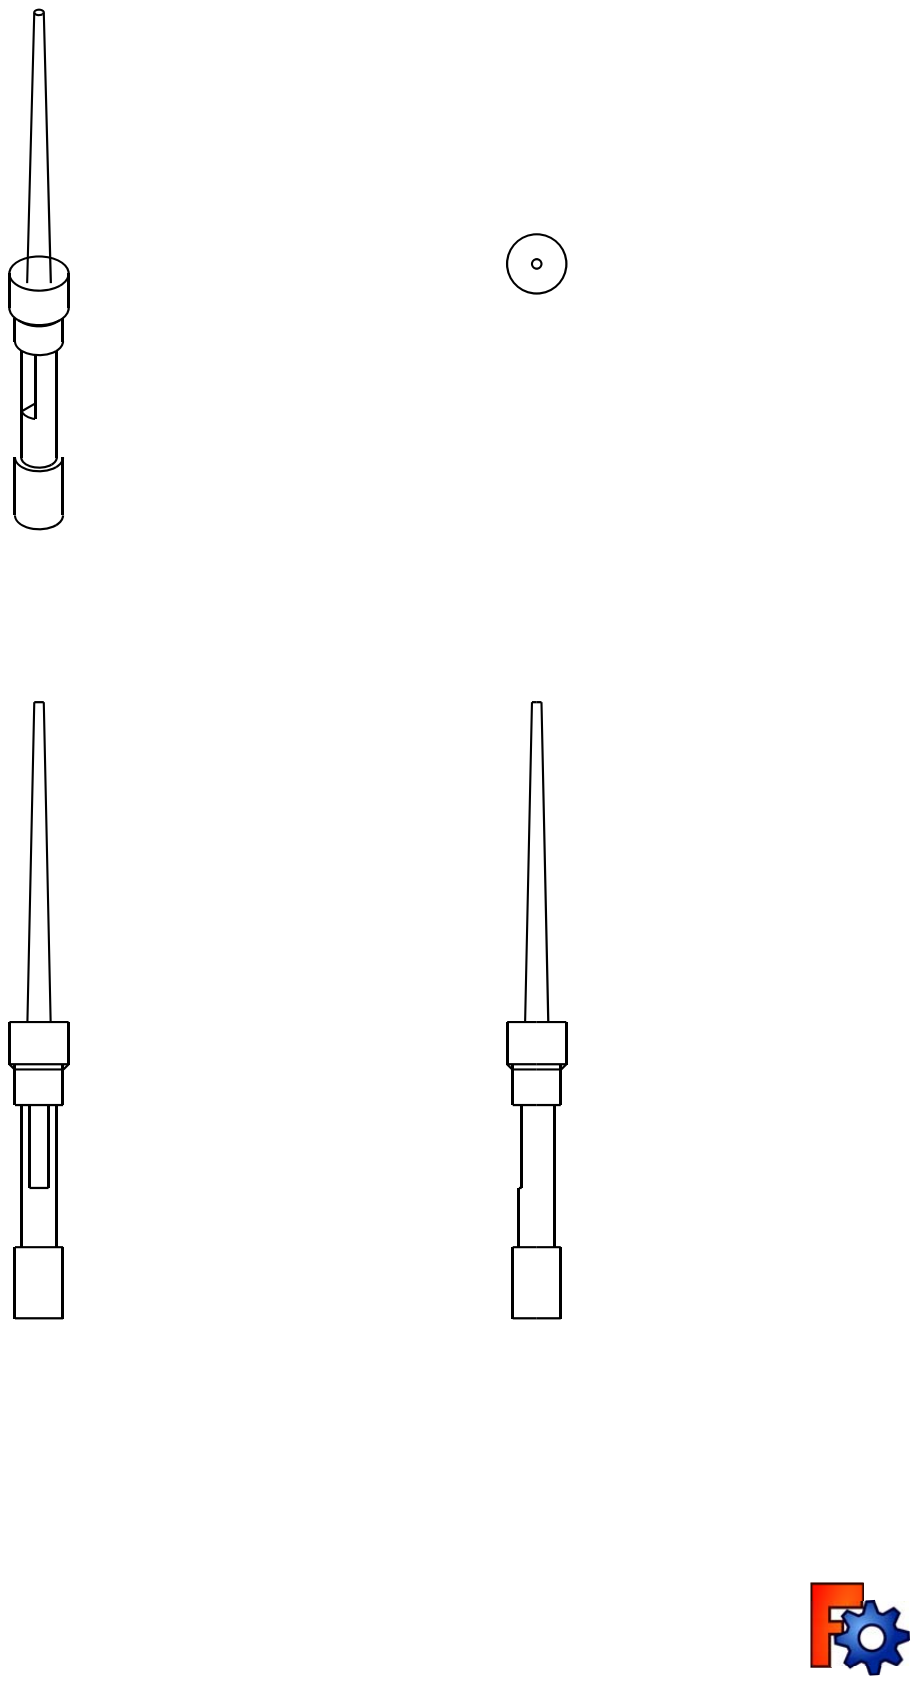
[picture p77: page 1]
