noaa-afsc-mace/FSVPAD-hydrophones/Technical documentation/Subsystemdrawings/Exploded1.pdf

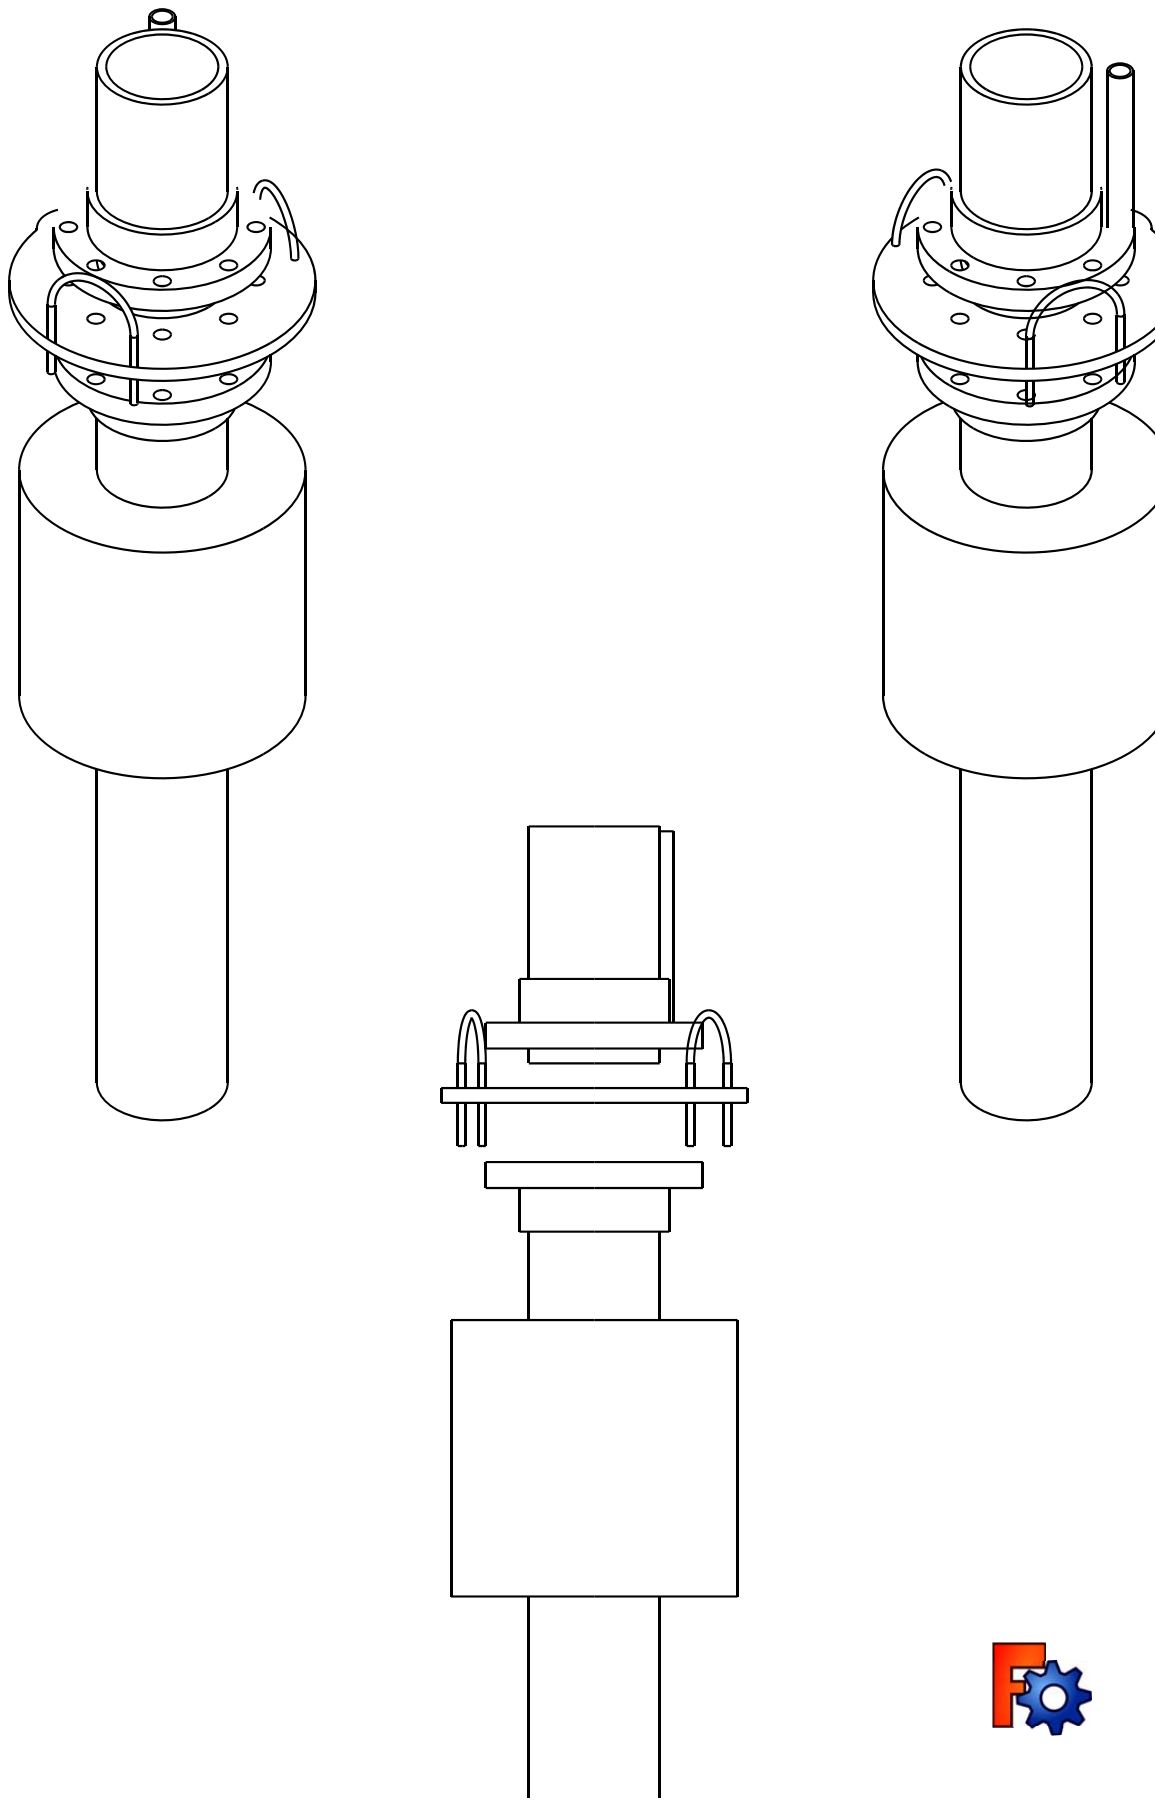
[picture p78: page 1]
